OfficeChromatography/2LabsToGo-Eco-Test/2LabsToGo-Eco-Hardware/Material-Lists/Prusa-basket.xlsx

Prusa basket
Amount | Part description | Unit price | Total price EUR
1 | Stepper motor Z-axis Right (MK3/S/+, MK2.5/S, MK2/S) | 32.68 | 32.68
1 | Hotend PTFE tube (MK2.5S, MK3S, MMU2S) | 1.08 | 1.08
2 | Timing pulley T16-2GT | 2.59 | 5.18
1 | Timing belt 2GT X-axis, MK3 | 4.87 | 4.87
1 | Timing belt 2GT X-axis, MINI | 3.35 | 3.35
1 | Trapezoid nut (i3, MK4, MMU2/2S/3) | 5.86 | 5.86
 |  | total | 53.02
 |  | incl. VAT | 63.09
