OfficeChromatography/2LabsToGo-Eco-Test/2LabsToGo-Eco-Hardware/Electronics/Digikey-basket_mainboard_plugs+cables_03-2026.xlsx

Digi-Key: Shopping Cart
Index | Quantity | Part Number | Manufacturer Part Number | Description | Customer Reference | Available | Backorder | Unit Price | Extended Price EUR
1 | 5 | 609-69145-206LF-ND | 69145-206LF | CONN SHUNT .100" 6POS GOLD | mumper motor driver | 5 | 0 | 0.59 | 2.95
2 | 1 | 609-69145-108LF-ND | 69145-108LF | JUMPER LOW PRO DR MULTI | jumper ISP to Pi | 1 | 0 | 1.22 | 1.22
3 | 1 | IDSD-20-D-02.00-ND | IDSD-20-D-02.00 | INSULATION DISPLACEMENT TERMINAL | GPIO cable | 0 | 1 | 12.35 | 12.35
4 | 1 | IDSS-14-D-05.00-ND | IDSS-14-D-05.00 | INSULATION DISPLACEMENT SOCKET C | Status LED board cable | 0 | 1 | 6.79 | 6.79
5 | 1 | 609-3887-ND | TJ0451560000G | TERM BLOCK PLUG 4POS 5.08MM | external port | 1 | 0 | 1.7 | 1.70
6 | 1 | 277-1164-ND | 1803604 | TERM BLOCK PLUG 5POS 3.81MM | plate holder | 1 | 0 | 5.21 | 5.21
7 | 1 | 277-1166-ND | 1803620 | TERM BLOCK PLUG 7POS 3.81MM | plug LEDs | 1 | 0 | 7.07 | 7.07
8 | 5 | 277-1161-ND | 1803578 | TERM BLOCK PLUG 2POS 3.81MM | pump, valves, light, nebulizer | 5 | 0 | 2.32 | 11.60
9 | 1 | 277-2414-ND | 1840405 | TERM BLOCK PLUG 6POS 3.50MM | plug mini-incubator | 1 | 0 | 6.75 | 6.75
