OfficeChromatography/2LabsToGo-Eco-Test/2LabsToGo-Eco-Hardware/Electronics/Digikey-basket_status-LED-board_03-2026.xlsx

Digi-Key: Shopping Cart
Index | Quantity | Part Number | Manufacturer Part Number | Description | Customer Reference | Available | Backorder | Unit Price | Extended Price EUR
1 | 3 | 754-1131-1-ND | APT2012SGC | LED GREEN CLEAR CHIP SMD | LED1, LED2, LED3 | 3 | 0 | 0.16 | 0.48
2 | 6 | 754-1133-1-ND | APT2012SURCK | LED RED CLEAR CHIP SMD | LED4, LED5, LED6, LED8, LED9, LED10 | 6 | 0 | 0.17 | 1.02
3 | 2 | 754-1134-1-ND | APT2012SYCK | LED YELLOW CLEAR CHIP SMD | LED7, LED11 | 0 | 2 | 0.17 | 0.34
4 | 1 | 19-Y2514-6002-SH14PSTHDR0.112GF-ND | Y2514-6002-SH 14P ST HDR 0.112 GF | 3M FOUR-WALL HEADER 2500 SERIES | SV1 | 1 | 0 | 1.02 | 1.02
