OfficeChromatography/2LabsToGo-Eco-Test/2LabsToGo-Eco-Hardware/Electronics/Digikey-basket_UV-LED-boards_03-2026.xlsx

Digi-Key: Warenkorb
Index | Menge | Teilenummer | Hersteller-Teilenummer | Beschreibung | Kundenreferenz | Verfügbar | Lieferrückstände | Stückpreis | Gesamtpreis EUR
1 | 4 | 1830-1187-1-ND | IN-C33CTNU2 | TOP VIEW 3535 3.5X3.5X2.0 | UV 365 nm LEDs | 4 | 0 | 5.92 | 23.68
2 | 4 | 4515-SA265-35030-SA1CT-ND | SA265-35030-SA1 | 260 - 270 NM, >30MW OUTPUT POWER | UV 265 nm LEDs | 4 | 0 | 3.85 | 15.40
3 | 10 | P17615CT-ND | ERJ-8BQF4R3V | RES SMD 4.3 OHM 1% 1/2W 1206 | UV 365 board, 8 needed | 10 | 0 | 0.124 | 1.24
4 | 10 | P20.0FCT-ND | ERJ-8ENF20R0V | RES SMD 20 OHM 1% 1/4W 1206 | UV 265 board, 4 needed | 10 | 0 | 0.07 | 0.70
