OfficeChromatography/2LabsToGo-Eco-Test/2LabsToGo-Eco-Hardware/3D-Parts/STL/tools/tool_ miniature_ball_ bearings.stl

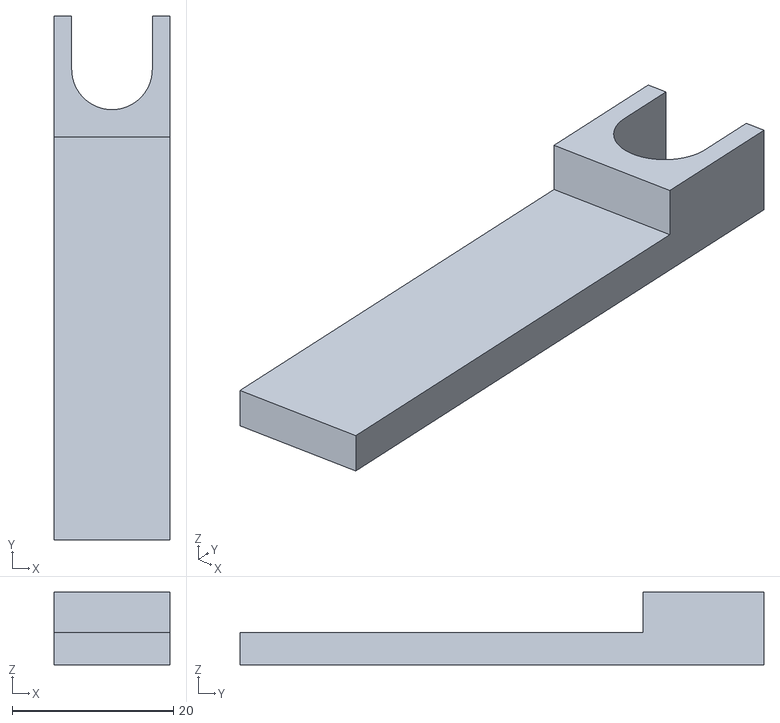
[picture p18: CAD file, 2026-04-15]
2LabsToGo-Eco-Hardware/3D-Parts/STL/tools/tool_ miniature_ball_ bearings.stl
14.4 x 65.0 x 9.00
