OfficeChromatography/2LabsToGo-Eco-Test/2LabsToGo-Eco-Hardware/3D-Parts/STL/x-axis/x-axis_cart-tensioner.stl

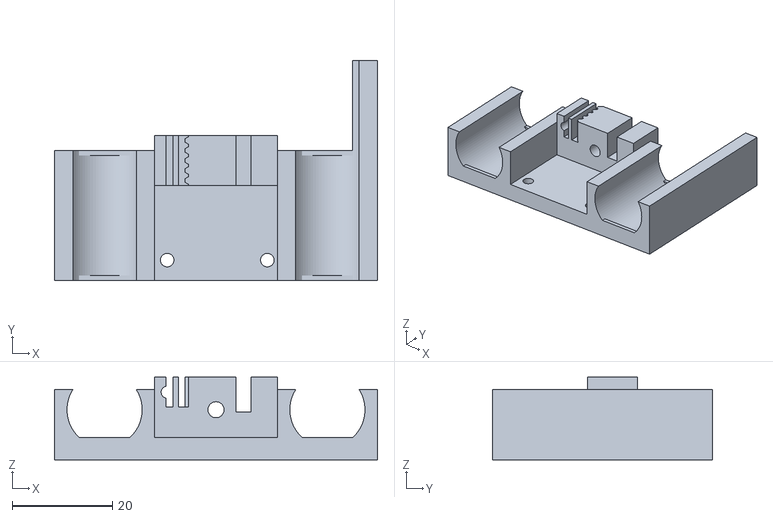
[picture p19: CAD file, 2026-04-15]
2LabsToGo-Eco-Hardware/3D-Parts/STL/x-axis/x-axis_cart-tensioner.stl
64.5 x 44.0 x 16.5
