OfficeChromatography/2LabsToGo-Eco-Test/2LabsToGo-Eco-Hardware/3D-Parts/STL/y-axis/y-axis_tensioner.stl

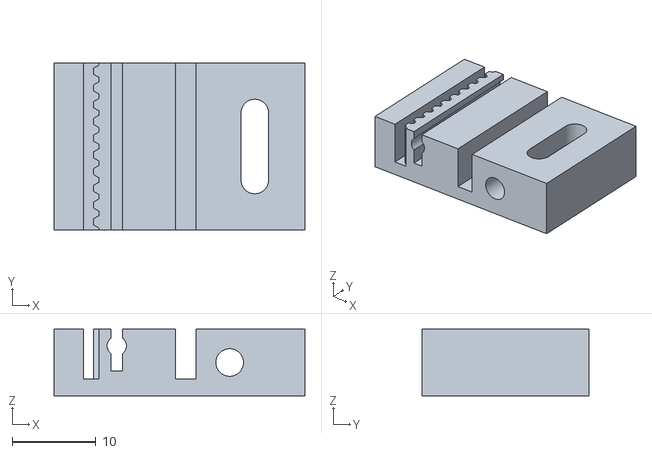
[picture p20: CAD file, 2026-04-15]
2LabsToGo-Eco-Hardware/3D-Parts/STL/y-axis/y-axis_tensioner.stl
30.0 x 20.0 x 8.00
