OfficeChromatography/2LabsToGo-Eco-Test/2LabsToGo-Eco-Hardware/3D-Parts/Aluminum-plates/alu-plate_plate-holder.step

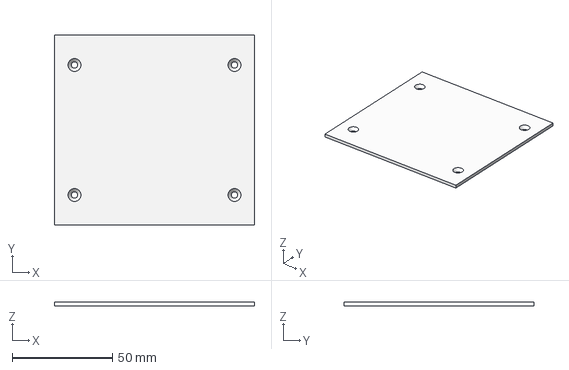
[picture p21: CAD file, 2026-04-15]
2LabsToGo-Eco-Hardware/3D-Parts/Aluminum-plates/alu-plate_plate-holder.step
100.0 x 95.0 x 2.00 mm
