OfficeChromatography/2LabsToGo-Eco-Test/2LabsToGo-Eco-Hardware/3D-Parts/DXF-panels/front.dxf

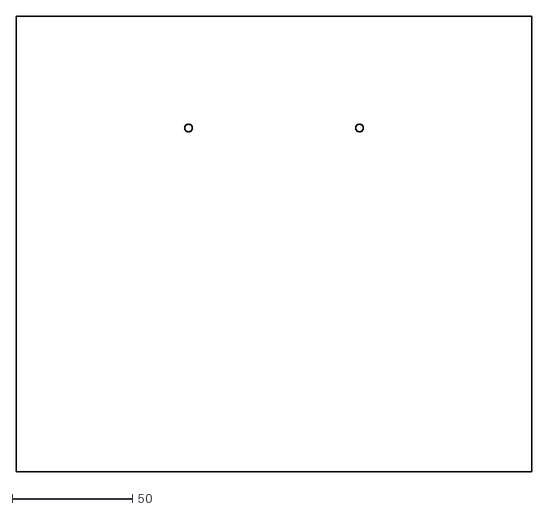
[picture p22: CAD file, 2026-04-15]
2LabsToGo-Eco-Hardware/3D-Parts/DXF-panels/front.dxf
214.0 x 189.0
