OfficeChromatography/2LabsToGo-Eco-Test/2LabsToGo-Eco-Hardware/3D-Parts/STL/autosampler/rinsing_vial.stl

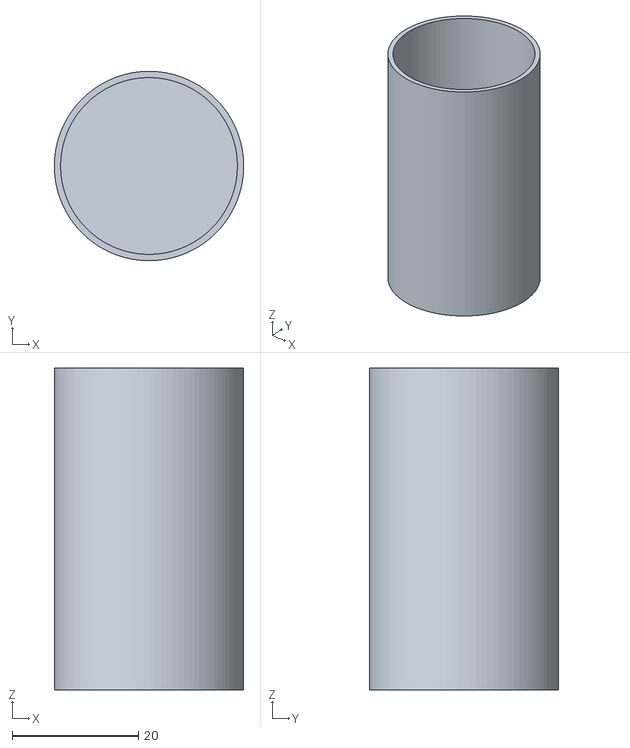
[picture p23: CAD file, 2026-04-15]
2LabsToGo-Eco-Hardware/3D-Parts/STL/autosampler/rinsing_vial.stl
30.0 x 30.0 x 51.0
