OfficeChromatography/2LabsToGo-Eco-Test/2LabsToGo-Eco-Hardware/3D-Parts/STL/camera_cabinet/camera_cabinet_top.stl

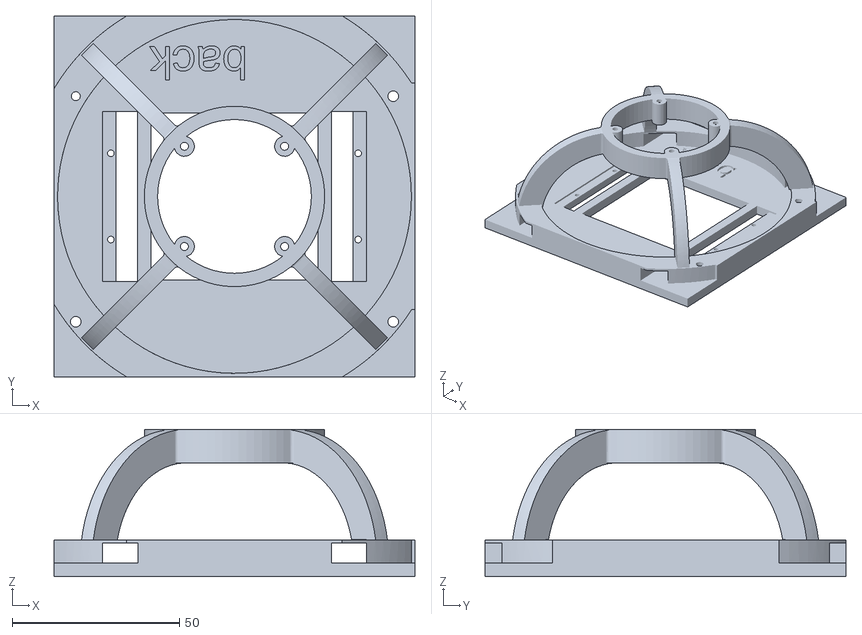
[picture p24: CAD file, 2026-04-15]
2LabsToGo-Eco-Hardware/3D-Parts/STL/camera_cabinet/camera_cabinet_top.stl
108.0 x 108.1 x 44.0
