OfficeChromatography/2LabsToGo-Eco-Test/2LabsToGo-Eco-Hardware/3D-Parts/STL/DC-power-jacket_housing/DC-power-jacket_housing_cover.stl

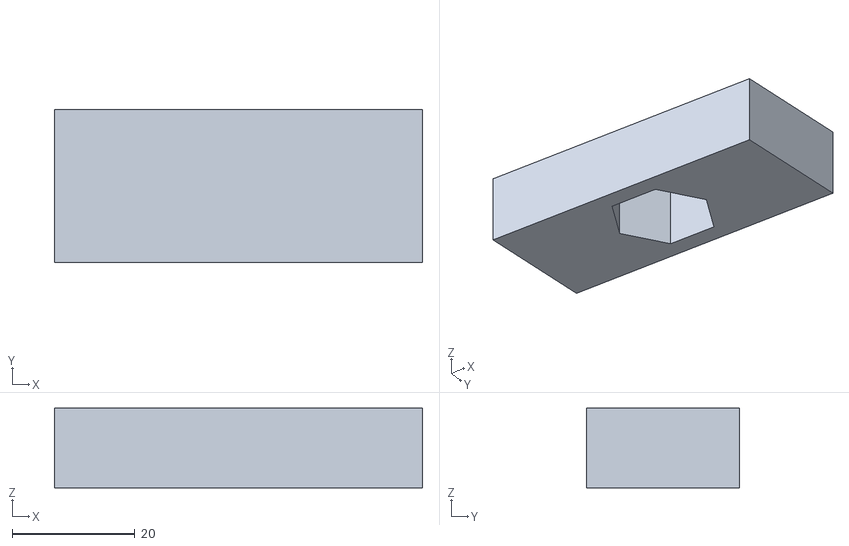
[picture p25: CAD file, 2026-04-15]
2LabsToGo-Eco-Hardware/3D-Parts/STL/DC-power-jacket_housing/DC-power-jacket_housing_cover.stl
60.0 x 25.0 x 13.0
