OfficeChromatography/2LabsToGo-Eco-Test/2LabsToGo-Eco-Hardware/3D-Parts/STL/e-axis/e-axis_connector_long.stl

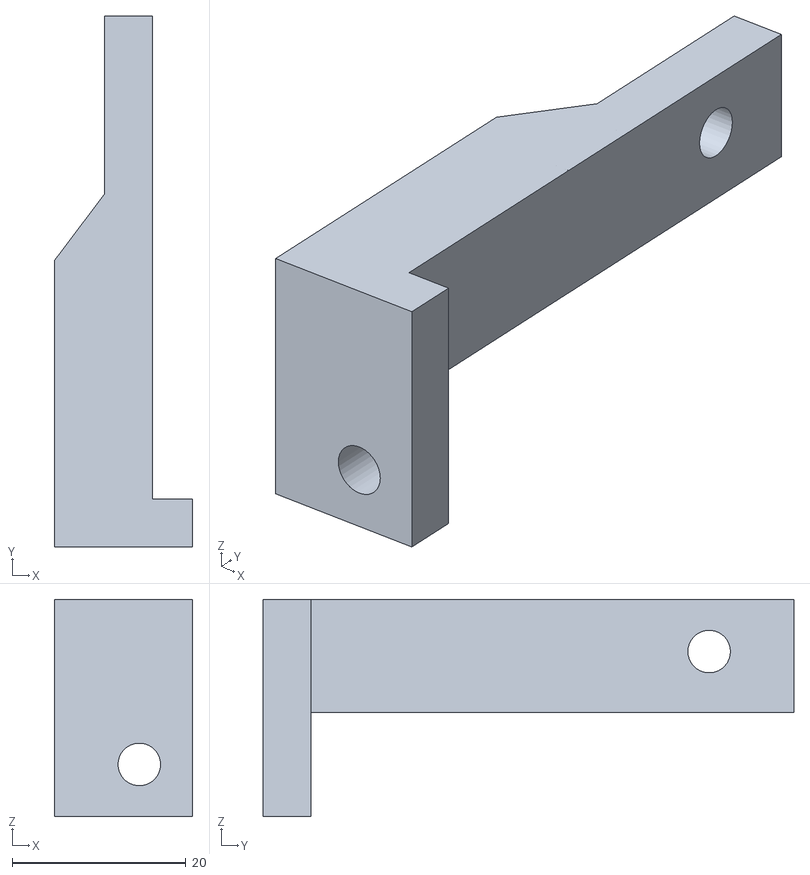
[picture p26: CAD file, 2026-04-15]
2LabsToGo-Eco-Hardware/3D-Parts/STL/e-axis/e-axis_connector_long.stl
15.9 x 61.1 x 25.0
