OfficeChromatography/2LabsToGo-Eco-Test/2LabsToGo-Eco-Hardware/3D-Parts/STL/electronic-box/electronic_box.stl

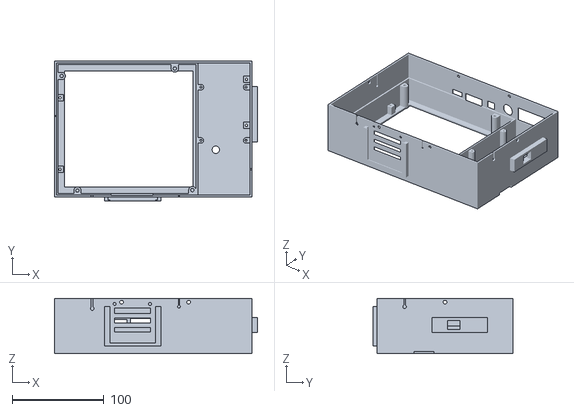
[picture p27: CAD file, 2026-04-20]
2LabsToGo-Eco-Hardware/3D-Parts/STL/electronic-box/electronic_box.stl
221.0 x 152.4 x 60.0
