OfficeChromatography/2LabsToGo-Eco-Test/2LabsToGo-Eco-Hardware/3D-Parts/STL/frames/frame_back_buttom.stl

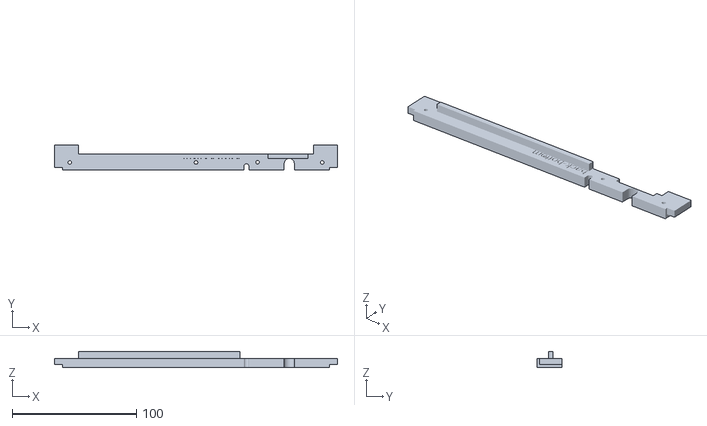
[picture p28: CAD file, 2026-04-20]
2LabsToGo-Eco-Hardware/3D-Parts/STL/frames/frame_back_buttom.stl
227.6 x 20.0 x 13.0
