OfficeChromatography/2LabsToGo-Eco-Test/2LabsToGo-Eco-Hardware/3D-Parts/STL/humidity-control/humidity_control_box-lid.stl

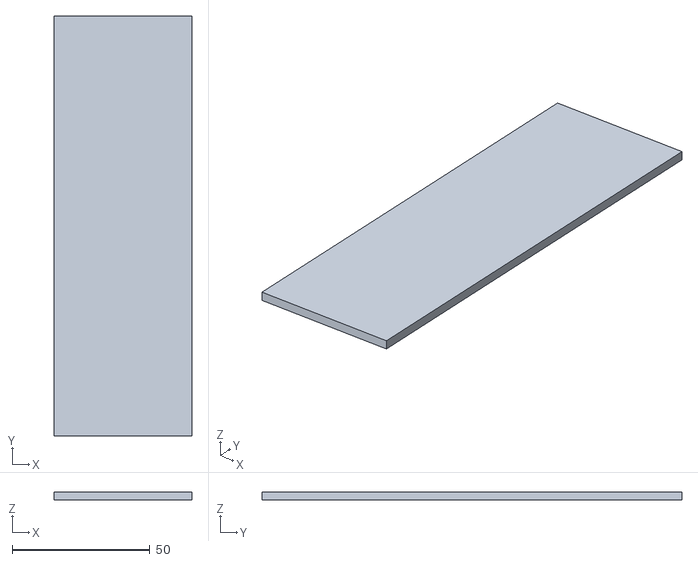
[picture p29: CAD file, 2026-04-15]
2LabsToGo-Eco-Hardware/3D-Parts/STL/humidity-control/humidity_control_box-lid.stl
50.0 x 152.0 x 3.00
