OfficeChromatography/2LabsToGo-Eco-Test/2LabsToGo-Eco-Hardware/3D-Parts/STL/mini-incubator/mini-incubator_inner_lid.stl

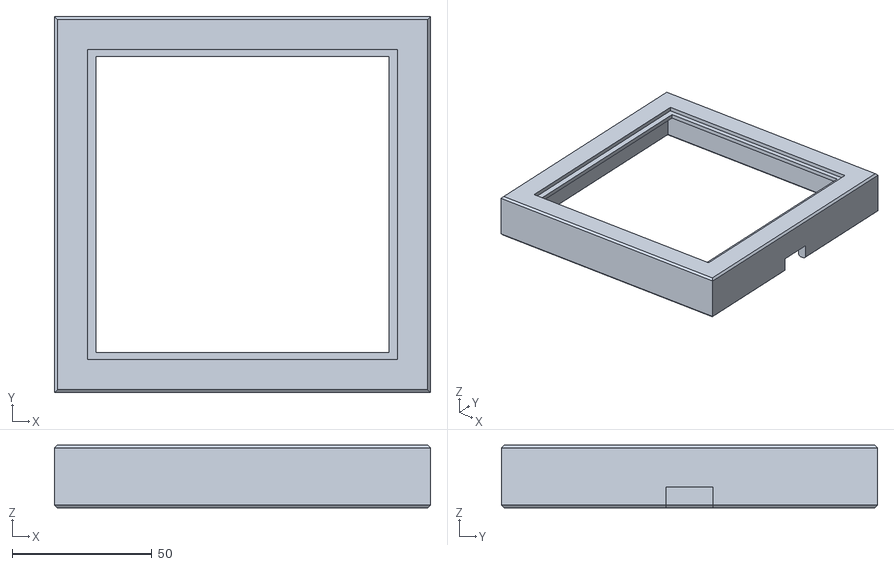
[picture p30: CAD file, 2026-04-15]
2LabsToGo-Eco-Hardware/3D-Parts/STL/mini-incubator/mini-incubator_inner_lid.stl
134.6 x 134.6 x 22.5
