OfficeChromatography/2LabsToGo-Eco-Test/2LabsToGo-Eco-Hardware/3D-Parts/STL/nebulizer/nebulizer_atomizer_part-1.stl

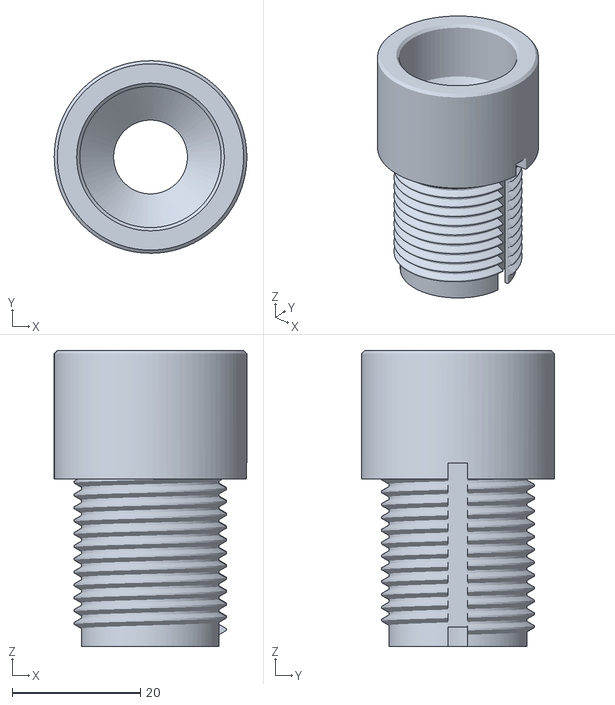
[picture p31: CAD file, 2026-04-20]
2LabsToGo-Eco-Hardware/3D-Parts/STL/nebulizer/nebulizer_atomizer_part-1.stl
30.0 x 30.0 x 46.1
