OfficeChromatography/2LabsToGo-Eco-Test/2LabsToGo-Eco-Hardware/3D-Parts/STL/panels/leg_inside.stl

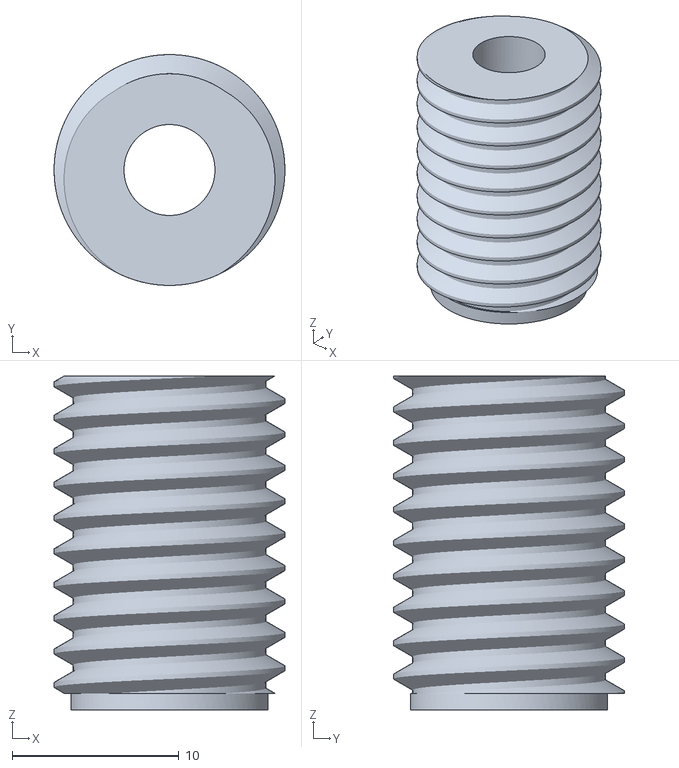
[picture p32: CAD file, 2026-04-15]
2LabsToGo-Eco-Hardware/3D-Parts/STL/panels/leg_inside.stl
13.8 x 13.8 x 20.0
