OfficeChromatography/2LabsToGo-Eco-Test/2LabsToGo-Eco-Hardware/3D-Parts/STL/plate-holder/multifunctional_plate_holder_cover_development.stl

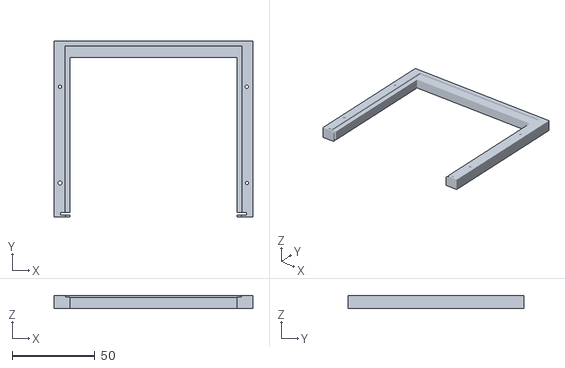
[picture p33: CAD file, 2026-04-15]
2LabsToGo-Eco-Hardware/3D-Parts/STL/plate-holder/multifunctional_plate_holder_cover_development.stl
120.0 x 106.0 x 8.00
