OfficeChromatography/2LabsToGo-Eco-Test/2LabsToGo-Eco-Hardware/3D-Parts/STL/syringe-pump/syringe-pump_clip.stl

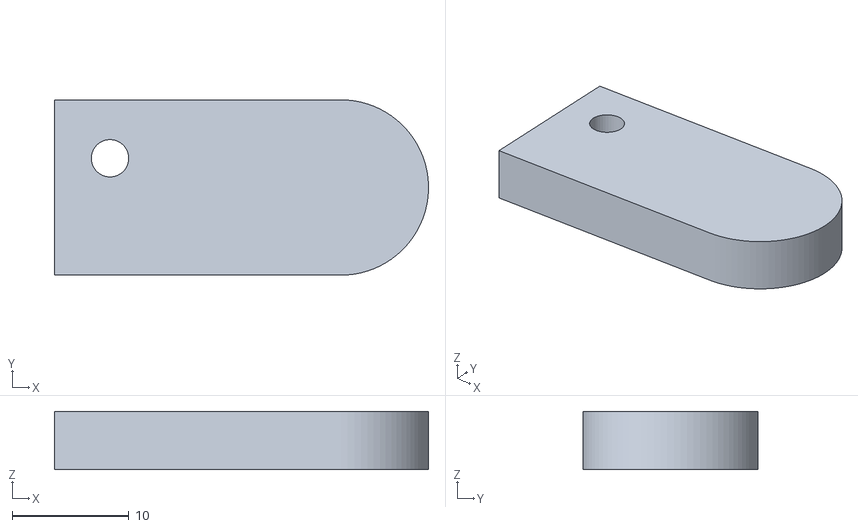
[picture p34: CAD file, 2026-04-15]
2LabsToGo-Eco-Hardware/3D-Parts/STL/syringe-pump/syringe-pump_clip.stl
32.0 x 15.0 x 5.00
