OfficeChromatography/2LabsToGo-Eco-Test/2LabsToGo-Eco-Hardware/3D-Parts/STL/tools/handle_for_thread_tap_M5.stl

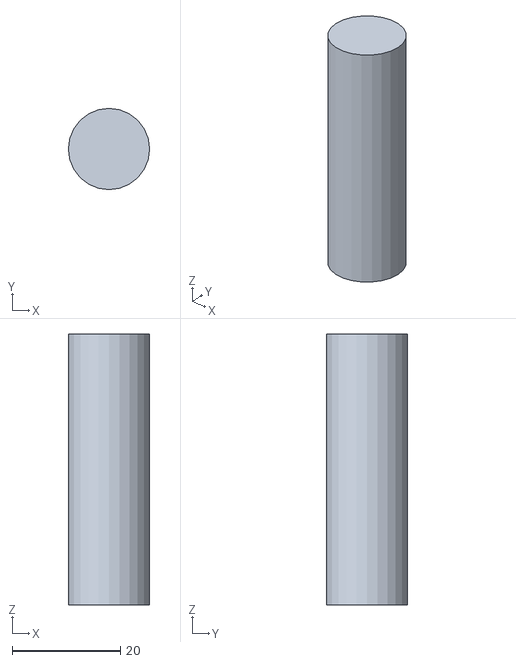
[picture p35: CAD file, 2026-04-15]
2LabsToGo-Eco-Hardware/3D-Parts/STL/tools/handle_for_thread_tap_M5.stl
15.0 x 15.0 x 50.0
