OfficeChromatography/2LabsToGo-Eco-Test/2LabsToGo-Eco-Hardware/3D-Parts/STL/x-axis/x-axis_cable_guide_top_right.stl

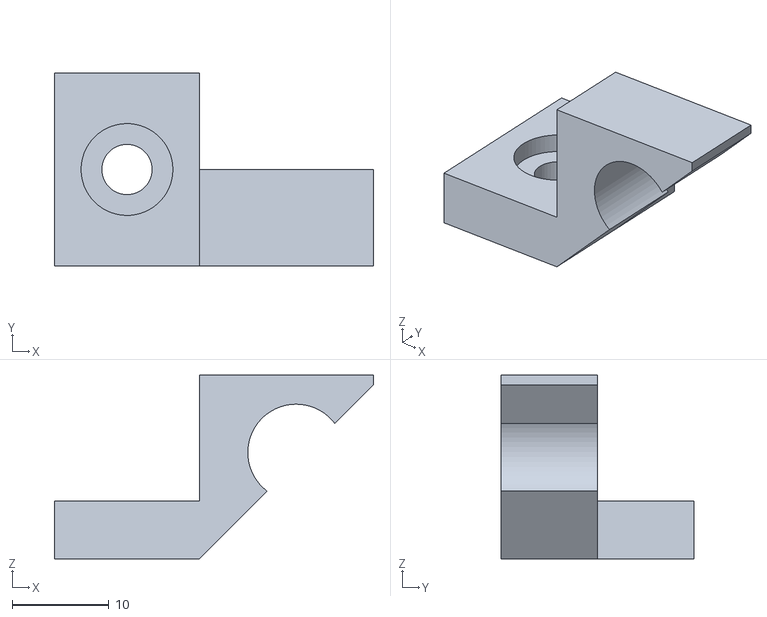
[picture p36: CAD file, 2026-04-15]
2LabsToGo-Eco-Hardware/3D-Parts/STL/x-axis/x-axis_cable_guide_top_right.stl
33.0 x 20.0 x 19.0
