OfficeChromatography/2LabsToGo-Eco-Test/2LabsToGo-Eco-Hardware/3D-Parts/STL/y-axis/y-axis_back.stl

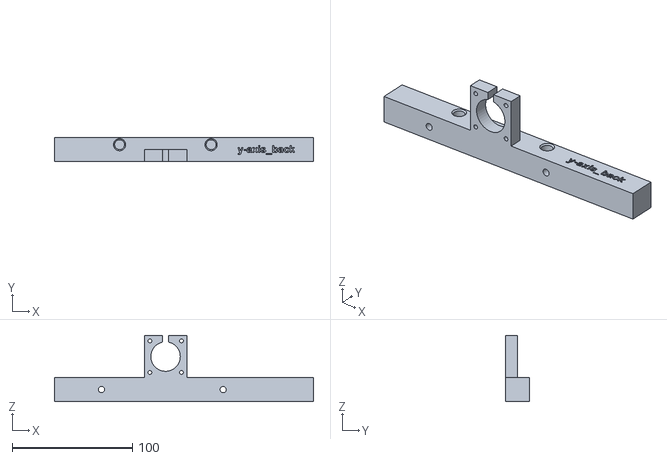
[picture p37: CAD file, 2026-04-15]
2LabsToGo-Eco-Hardware/3D-Parts/STL/y-axis/y-axis_back.stl
215.0 x 20.0 x 55.0
