OfficeChromatography/2LabsToGo-Eco-Test/2LabsToGo-Eco-Hardware/3D-Parts/DXF-panels/top_front.dxf

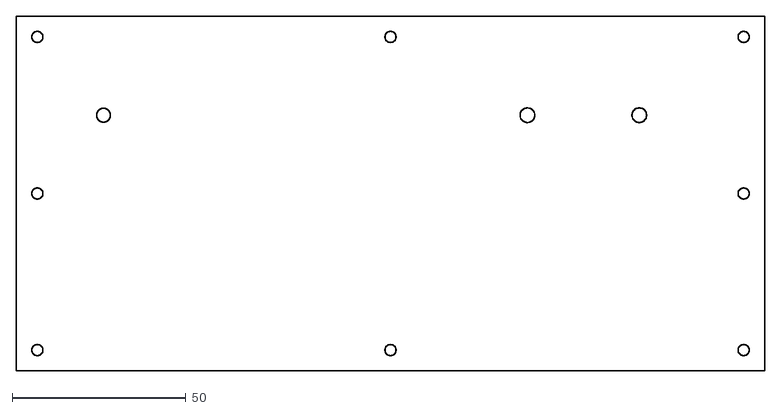
[picture p38: CAD file, 2026-04-15]
2LabsToGo-Eco-Hardware/3D-Parts/DXF-panels/top_front.dxf
215.0 x 102.0
