OfficeChromatography/2LabsToGo-Eco-Test/2LabsToGo-Eco-Hardware/3D-Parts/STL/autosampler/autosampler_distance-tool.stl

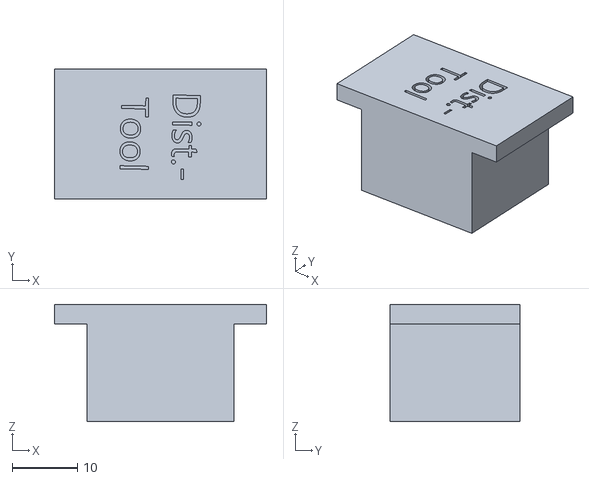
[picture p39: CAD file, 2026-04-15]
2LabsToGo-Eco-Hardware/3D-Parts/STL/autosampler/autosampler_distance-tool.stl
32.5 x 20.0 x 18.0
