OfficeChromatography/2LabsToGo-Eco-Test/2LabsToGo-Eco-Hardware/3D-Parts/STL/camera_cabinet/camera_cabinet.stl

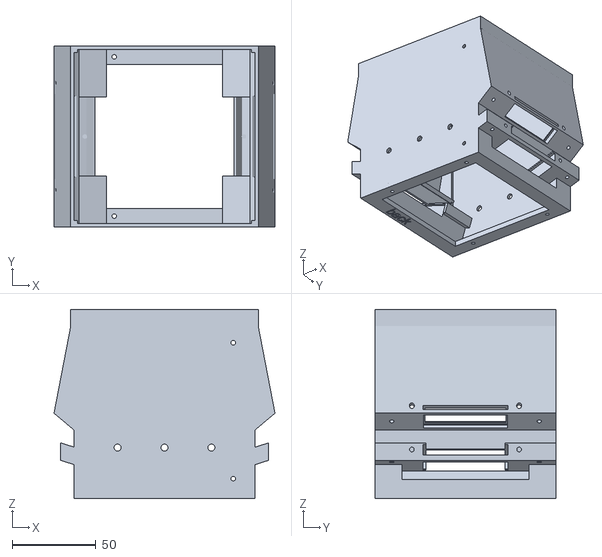
[picture p40: CAD file, 2026-04-15]
2LabsToGo-Eco-Hardware/3D-Parts/STL/camera_cabinet/camera_cabinet.stl
131.8 x 108.0 x 113.0
