OfficeChromatography/2LabsToGo-Eco-Test/2LabsToGo-Eco-Hardware/3D-Parts/STL/e-axis/e-axis_3way_valve_holder.stl

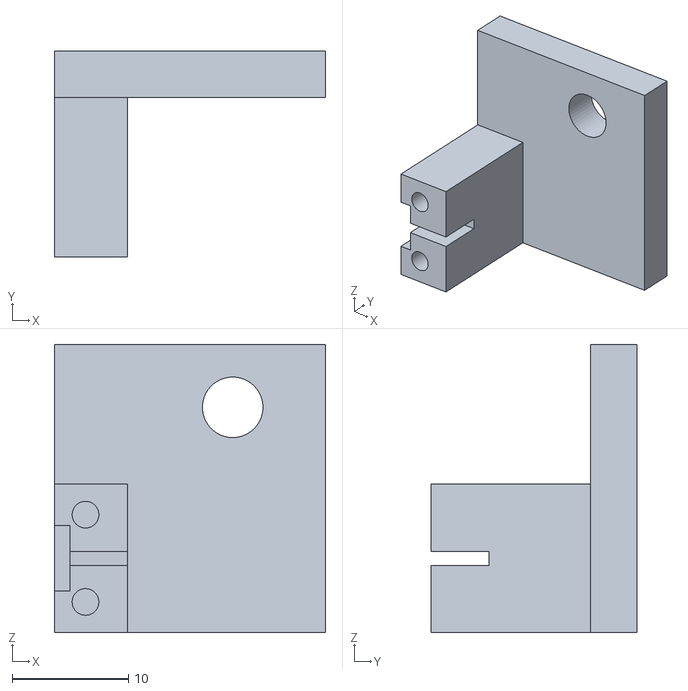
[picture p41: CAD file, 2026-04-15]
2LabsToGo-Eco-Hardware/3D-Parts/STL/e-axis/e-axis_3way_valve_holder.stl
23.3 x 17.7 x 24.8
