OfficeChromatography/2LabsToGo-Eco-Test/2LabsToGo-Eco-Hardware/3D-Parts/STL/electronic-box/electronic_box_frame-part1.stl

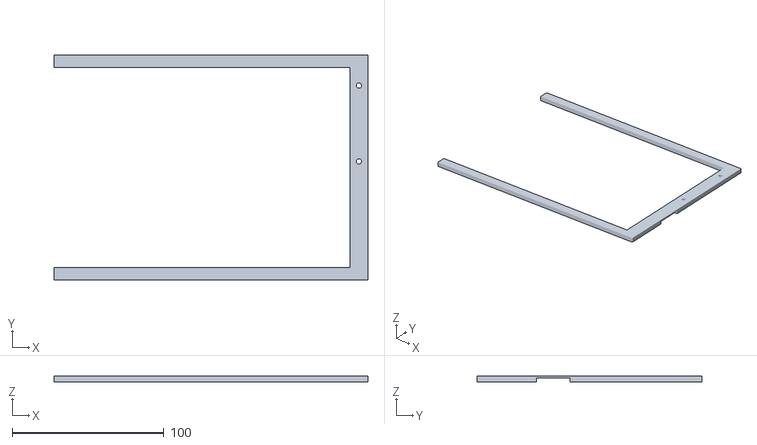
[picture p42: CAD file, 2026-04-20]
2LabsToGo-Eco-Hardware/3D-Parts/STL/electronic-box/electronic_box_frame-part1.stl
207.0 x 148.0 x 4.00
