OfficeChromatography/2LabsToGo-Eco-Test/2LabsToGo-Eco-Hardware/3D-Parts/STL/frames/frame_front.stl

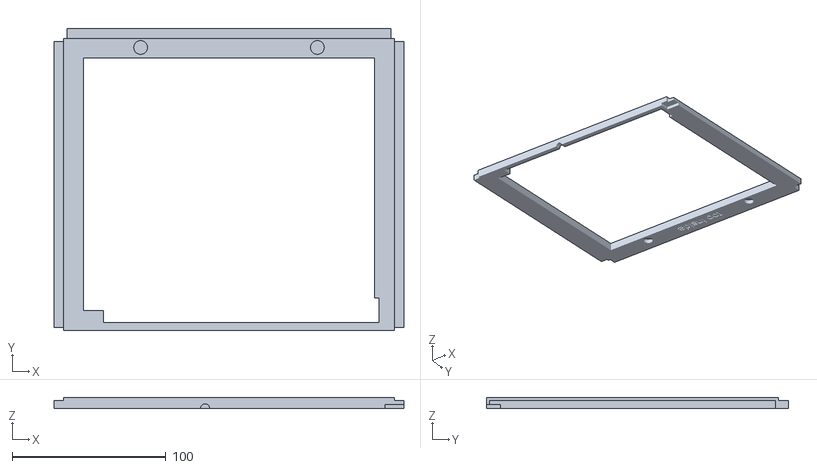
[picture p43: CAD file, 2026-04-15]
2LabsToGo-Eco-Hardware/3D-Parts/STL/frames/frame_front.stl
227.6 x 196.3 x 7.00
