OfficeChromatography/2LabsToGo-Eco-Test/2LabsToGo-Eco-Hardware/3D-Parts/STL/humidity-control/humidity_control_drawer.stl

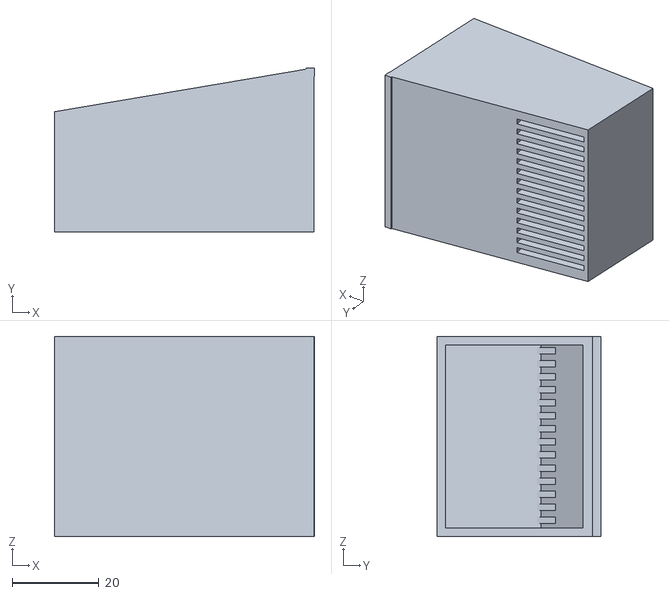
[picture p44: CAD file, 2026-04-15]
2LabsToGo-Eco-Hardware/3D-Parts/STL/humidity-control/humidity_control_drawer.stl
59.8 x 37.8 x 46.0
