OfficeChromatography/2LabsToGo-Eco-Test/2LabsToGo-Eco-Hardware/3D-Parts/STL/mini-incubator/mini-incubator_feet.stl

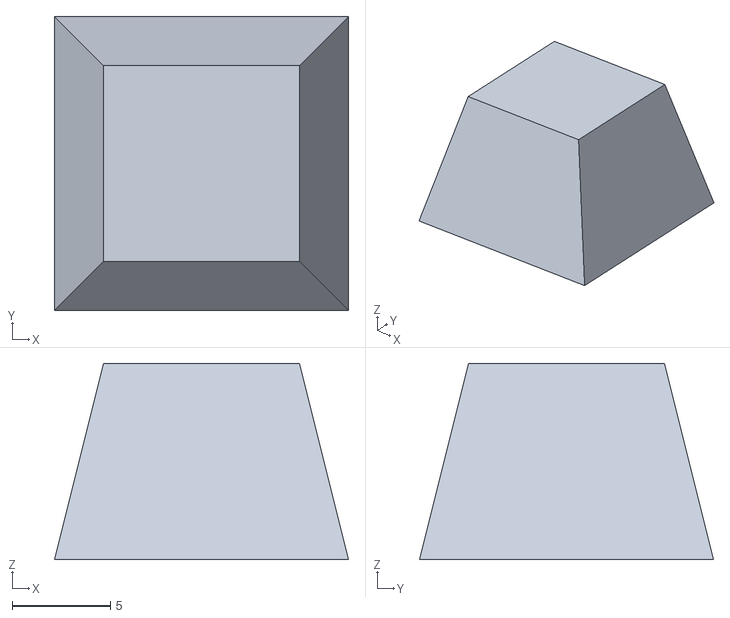
[picture p45: CAD file, 2026-04-15]
2LabsToGo-Eco-Hardware/3D-Parts/STL/mini-incubator/mini-incubator_feet.stl
15.0 x 15.0 x 10.0
