OfficeChromatography/2LabsToGo-Eco-Test/2LabsToGo-Eco-Hardware/3D-Parts/STL/mini-shaker/mini-shaker_hood.stl

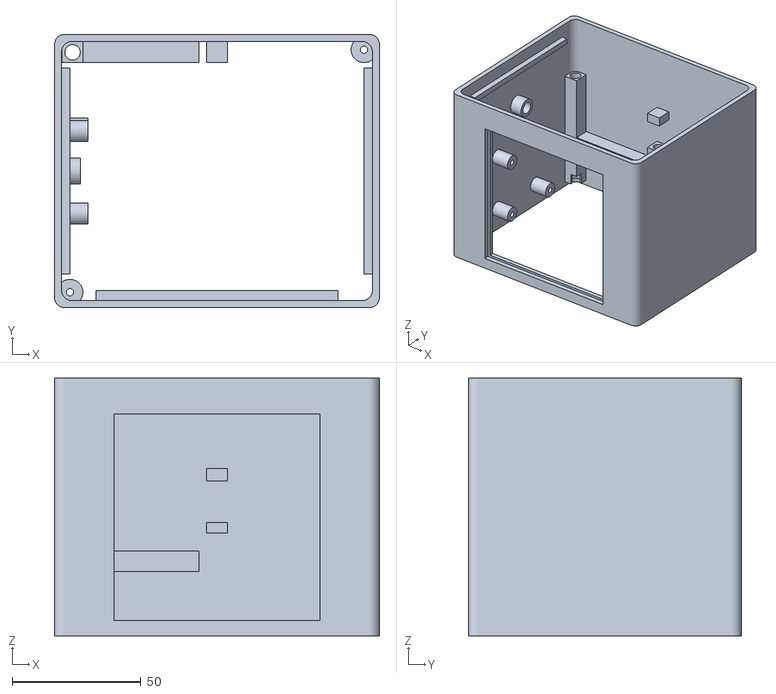
[picture p46: CAD file, 2026-04-15]
2LabsToGo-Eco-Hardware/3D-Parts/STL/mini-shaker/mini-shaker_hood.stl
126.0 x 106.0 x 100.0
