OfficeChromatography/2LabsToGo-Eco-Test/2LabsToGo-Eco-Hardware/3D-Parts/STL/nebulizer/nebulizer_atomizer_part-2.stl

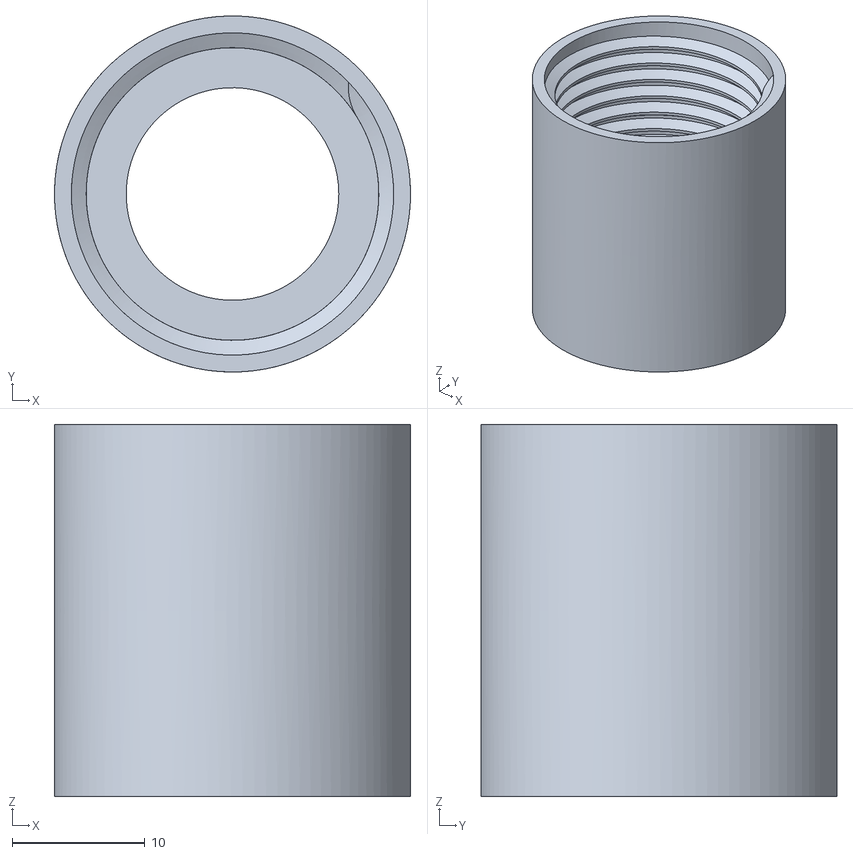
[picture p47: CAD file, 2026-04-20]
2LabsToGo-Eco-Hardware/3D-Parts/STL/nebulizer/nebulizer_atomizer_part-2.stl
26.8 x 26.8 x 28.0
