OfficeChromatography/2LabsToGo-Eco-Test/2LabsToGo-Eco-Hardware/3D-Parts/STL/panels/cover_z1_motor.stl

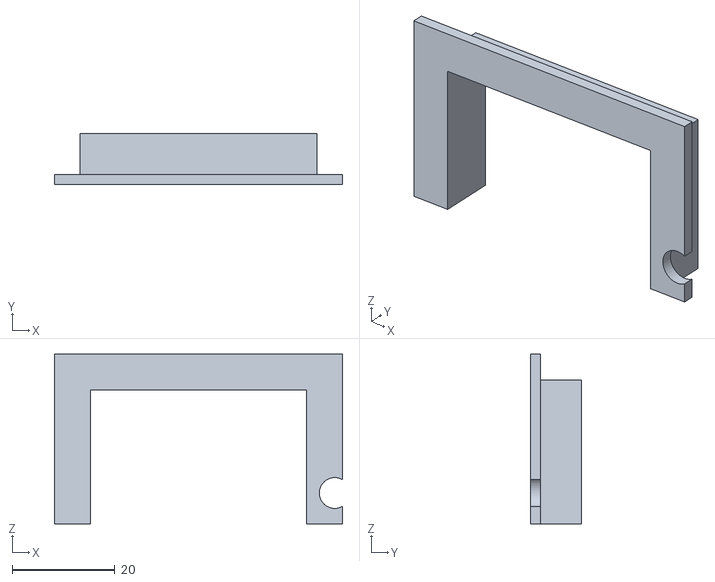
[picture p48: CAD file, 2026-04-15]
2LabsToGo-Eco-Hardware/3D-Parts/STL/panels/cover_z1_motor.stl
56.0 x 10.0 x 33.0
