OfficeChromatography/2LabsToGo-Eco-Test/2LabsToGo-Eco-Hardware/3D-Parts/STL/plate-holder/plate-holder_backlight_front.stl

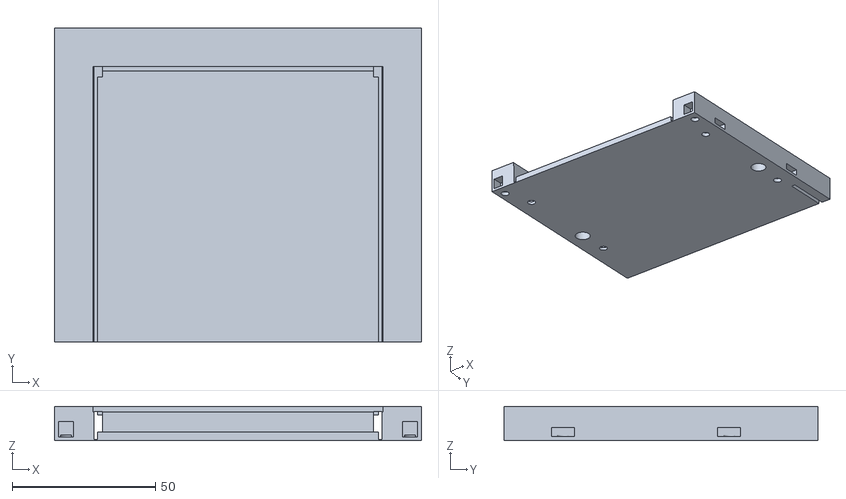
[picture p49: CAD file, 2026-04-15]
2LabsToGo-Eco-Hardware/3D-Parts/STL/plate-holder/plate-holder_backlight_front.stl
128.0 x 109.5 x 12.0
