OfficeChromatography/2LabsToGo-Eco-Test/2LabsToGo-Eco-Hardware/3D-Parts/STL/syringe-pump/syringe-pump_pusher_base.stl

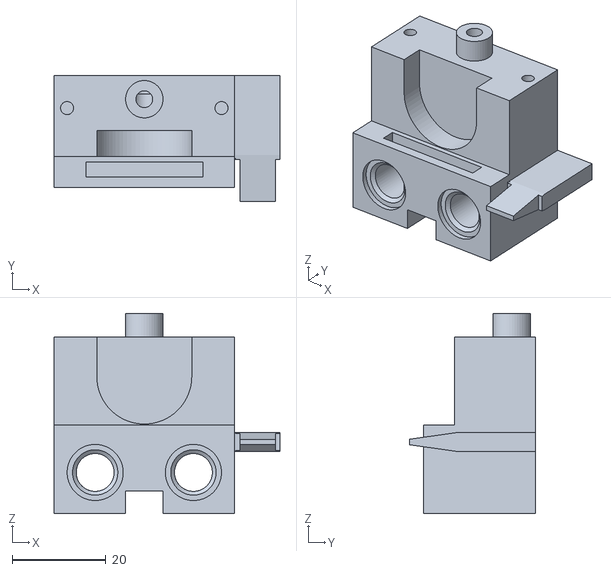
[picture p50: CAD file, 2026-04-15]
2LabsToGo-Eco-Hardware/3D-Parts/STL/syringe-pump/syringe-pump_pusher_base.stl
48.3 x 27.0 x 42.8
