OfficeChromatography/2LabsToGo-Eco-Test/2LabsToGo-Eco-Hardware/3D-Parts/STL/tools/needle-wrench_round.stl

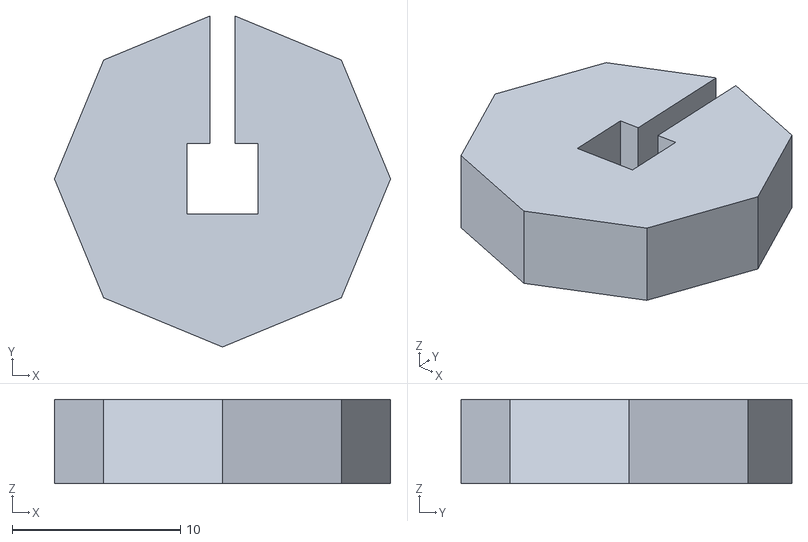
[picture p51: CAD file, 2026-04-15]
2LabsToGo-Eco-Hardware/3D-Parts/STL/tools/needle-wrench_round.stl
20.0 x 19.7 x 5.00
