OfficeChromatography/2LabsToGo-Eco-Test/2LabsToGo-Eco-Hardware/3D-Parts/STL/x-axis/x-axis_right.stl

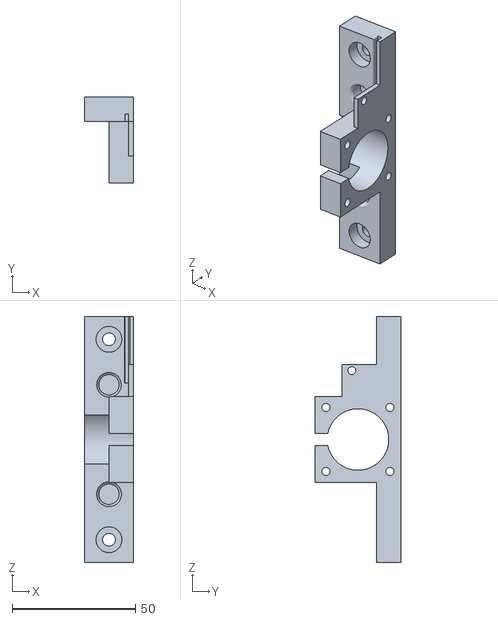
[picture p52: CAD file, 2026-04-15]
2LabsToGo-Eco-Hardware/3D-Parts/STL/x-axis/x-axis_right.stl
20.0 x 35.0 x 100.0
