OfficeChromatography/2LabsToGo-Eco-Test/2LabsToGo-Eco-Hardware/3D-Parts/STL/y-axis/cork.stl

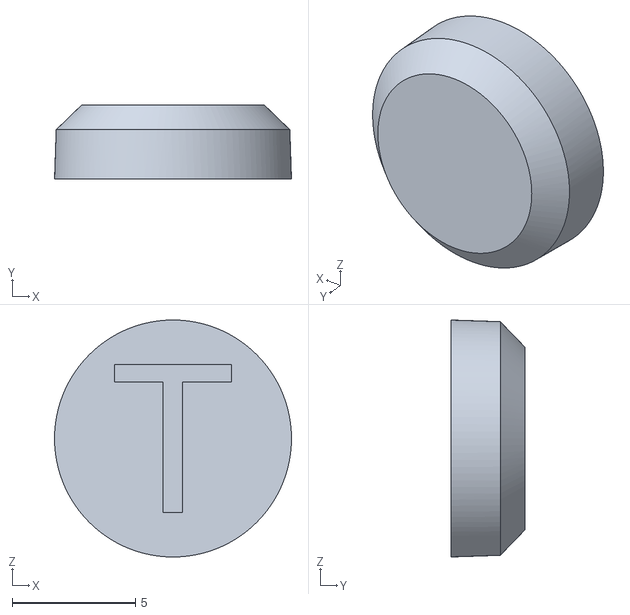
[picture p53: CAD file, 2026-04-15]
2LabsToGo-Eco-Hardware/3D-Parts/STL/y-axis/cork.stl
9.60 x 3.00 x 9.60
