OfficeChromatography/2LabsToGo-Eco-Test/2LabsToGo-Eco-Hardware/3D-Parts/DXF-panels/back.dxf

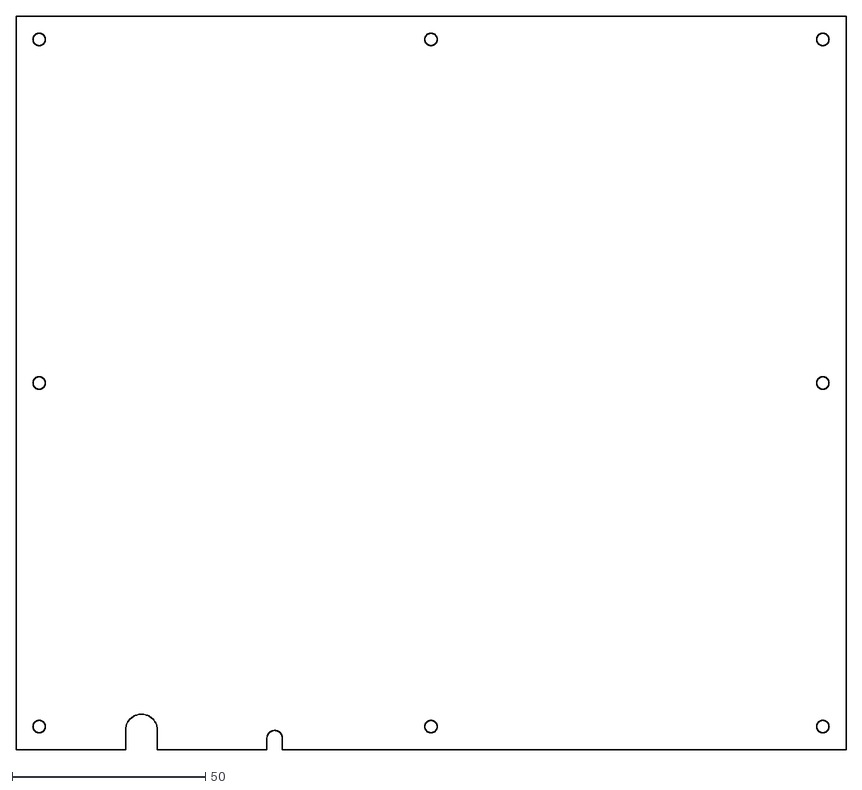
[picture p54: CAD file, 2026-04-15]
2LabsToGo-Eco-Hardware/3D-Parts/DXF-panels/back.dxf
215.0 x 190.0
