OfficeChromatography/2LabsToGo-Eco-Test/2LabsToGo-Eco-Hardware/3D-Parts/STL/autosampler/autosampler_slider_tip.stl

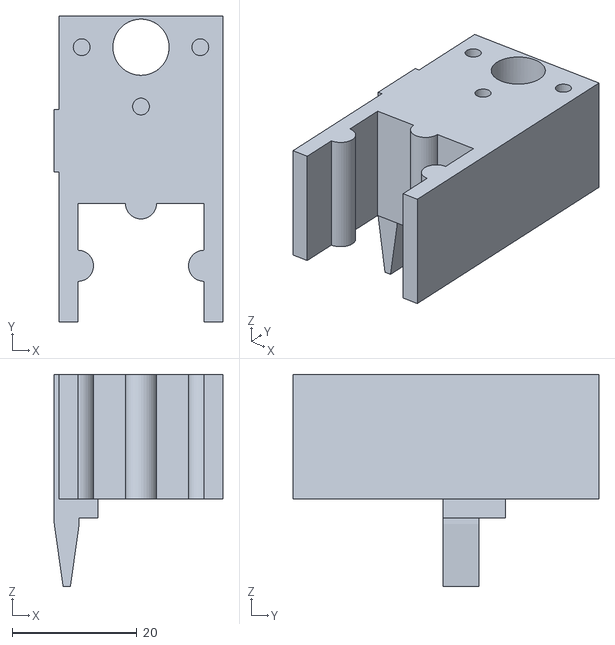
[picture p55: CAD file, 2026-04-15]
2LabsToGo-Eco-Hardware/3D-Parts/STL/autosampler/autosampler_slider_tip.stl
27.0 x 49.0 x 34.0
