OfficeChromatography/2LabsToGo-Eco-Test/2LabsToGo-Eco-Hardware/3D-Parts/STL/camera_cabinet/camera-cabinet_holder.stl

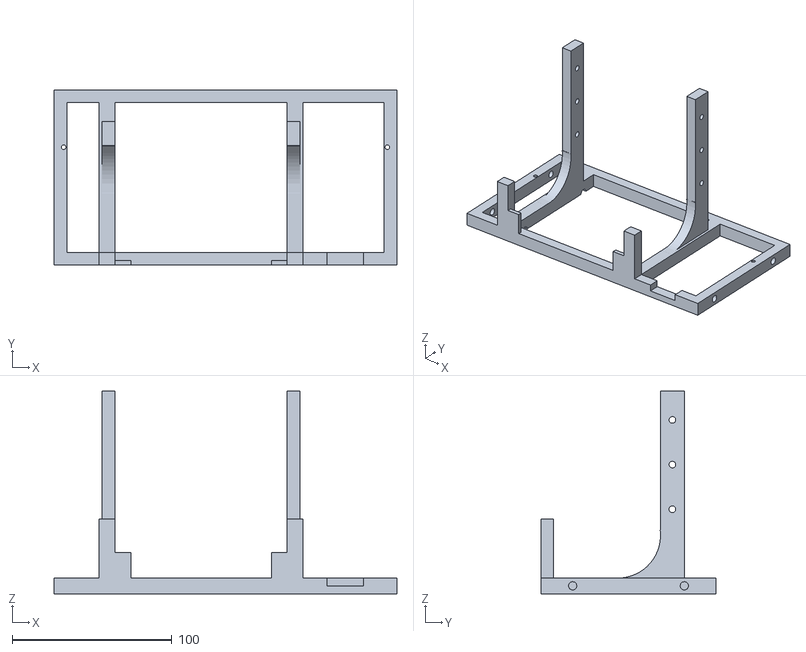
[picture p56: CAD file, 2026-04-15]
2LabsToGo-Eco-Hardware/3D-Parts/STL/camera_cabinet/camera-cabinet_holder.stl
215.0 x 110.0 x 127.0
