OfficeChromatography/2LabsToGo-Eco-Test/2LabsToGo-Eco-Hardware/3D-Parts/STL/e-axis/e-axis_needle_pusher.stl

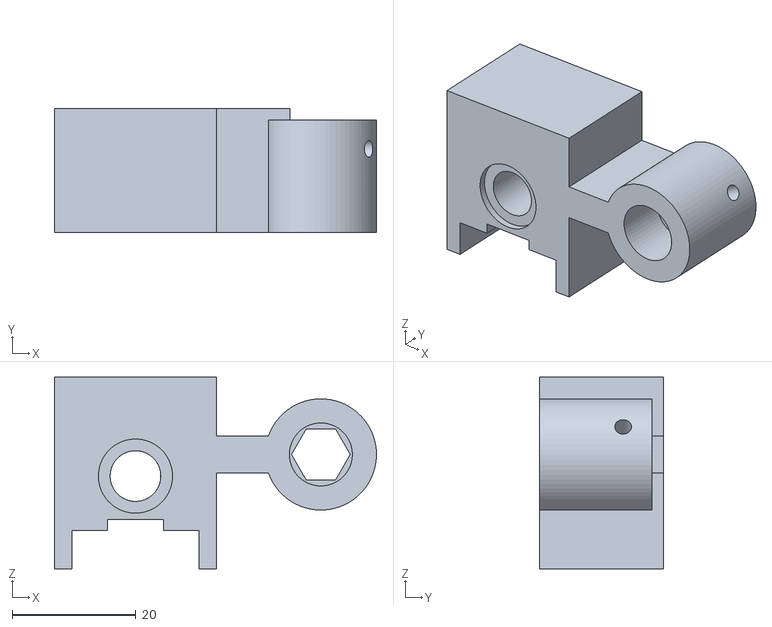
[picture p57: CAD file, 2026-04-15]
2LabsToGo-Eco-Hardware/3D-Parts/STL/e-axis/e-axis_needle_pusher.stl
52.1 x 20.0 x 31.0
