OfficeChromatography/2LabsToGo-Eco-Test/2LabsToGo-Eco-Hardware/3D-Parts/STL/electronic-box/electronic-box_cover.stl

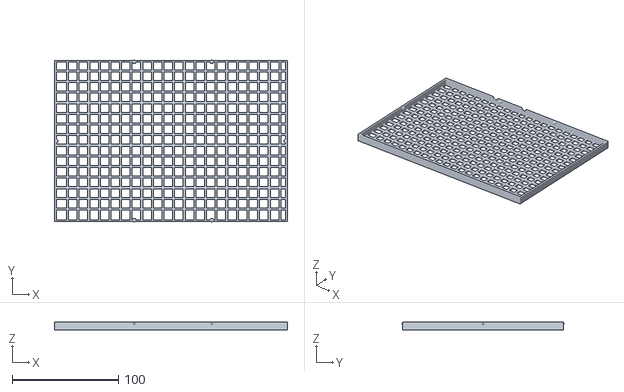
[picture p58: CAD file, 2026-04-15]
2LabsToGo-Eco-Hardware/3D-Parts/STL/electronic-box/electronic-box_cover.stl
219.5 x 152.5 x 8.00
