OfficeChromatography/2LabsToGo-Eco-Test/2LabsToGo-Eco-Hardware/3D-Parts/STL/humidity-control/humidity_control_drawer-handle.stl

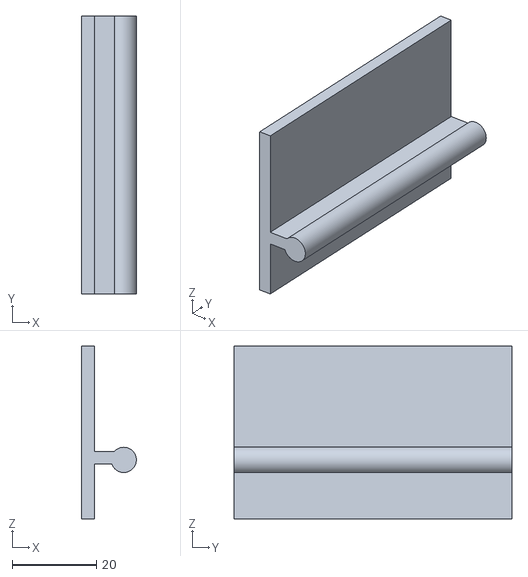
[picture p60: CAD file, 2026-04-15]
2LabsToGo-Eco-Hardware/3D-Parts/STL/humidity-control/humidity_control_drawer-handle.stl
13.0 x 66.0 x 41.0
