OfficeChromatography/2LabsToGo-Eco-Test/2LabsToGo-Eco-Hardware/3D-Parts/STL/mini-incubator/mini-incubator_outer_bottom.stl

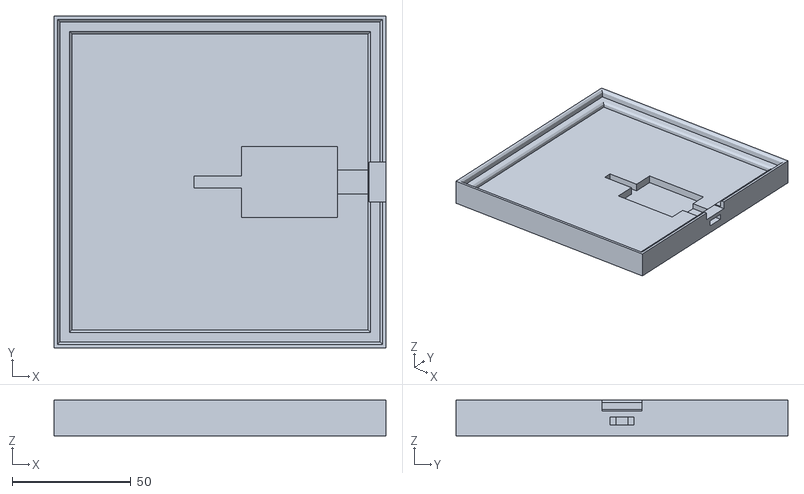
[picture p61: CAD file, 2026-04-15]
2LabsToGo-Eco-Hardware/3D-Parts/STL/mini-incubator/mini-incubator_outer_bottom.stl
140.0 x 140.0 x 15.0
