OfficeChromatography/2LabsToGo-Eco-Test/2LabsToGo-Eco-Hardware/3D-Parts/STL/mini-shaker/heated_hood_cable_support.stl

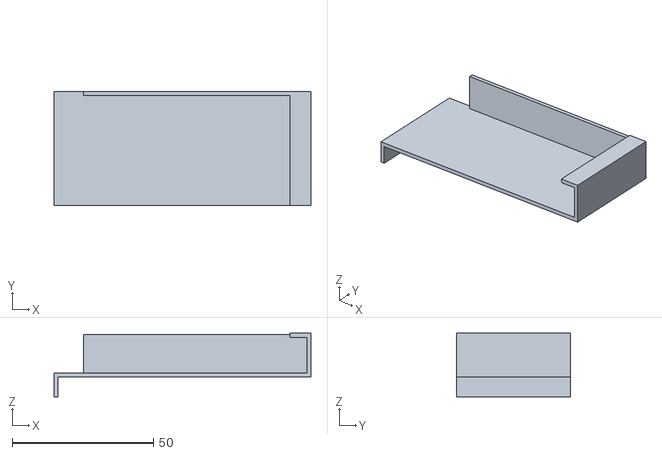
[picture p62: CAD file, 2026-04-15]
2LabsToGo-Eco-Hardware/3D-Parts/STL/mini-shaker/heated_hood_cable_support.stl
91.0 x 40.5 x 22.5
