OfficeChromatography/2LabsToGo-Eco-Test/2LabsToGo-Eco-Hardware/3D-Parts/STL/nebulizer/nebulizer_chamber_lid.stl

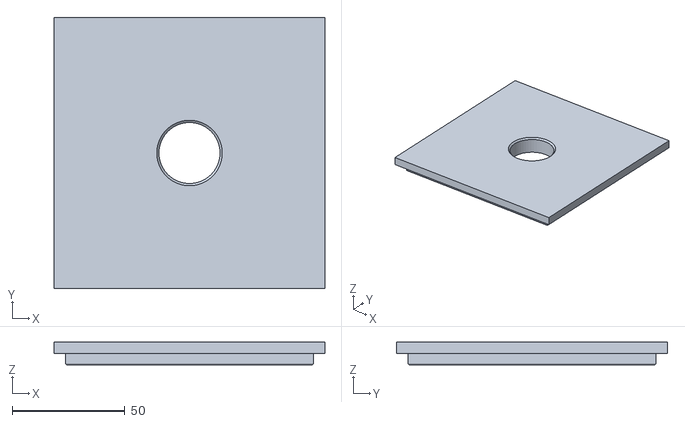
[picture p63: CAD file, 2026-04-15]
2LabsToGo-Eco-Hardware/3D-Parts/STL/nebulizer/nebulizer_chamber_lid.stl
120.0 x 120.0 x 10.0
