OfficeChromatography/2LabsToGo-Eco-Test/2LabsToGo-Eco-Hardware/3D-Parts/STL/panels/cover_autosampler_mounting_profile.stl

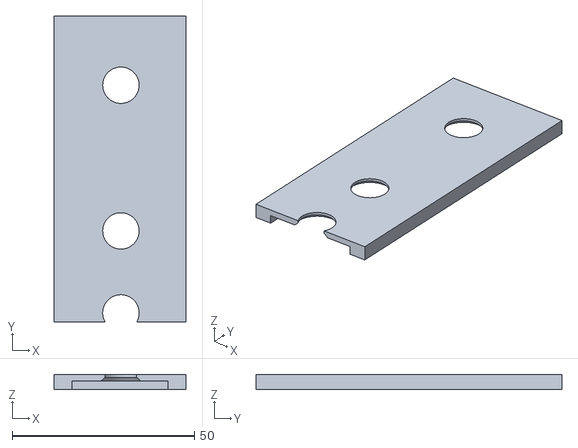
[picture p64: CAD file, 2026-04-15]
2LabsToGo-Eco-Hardware/3D-Parts/STL/panels/cover_autosampler_mounting_profile.stl
36.2 x 84.0 x 4.00
