OfficeChromatography/2LabsToGo-Eco-Test/2LabsToGo-Eco-Hardware/3D-Parts/STL/syringe-pump/syringe-pump_syringe_holder_adapter_5mL.stl

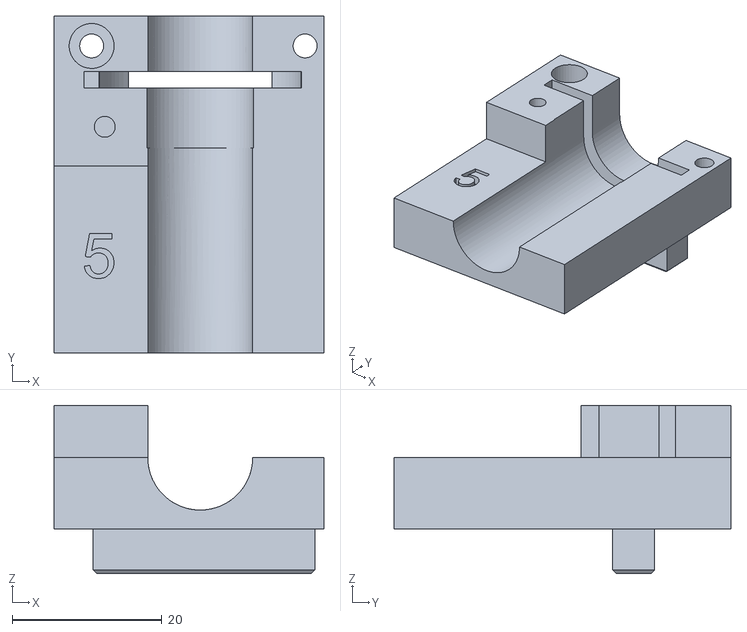
[picture p66: CAD file, 2026-04-15]
2LabsToGo-Eco-Hardware/3D-Parts/STL/syringe-pump/syringe-pump_syringe_holder_adapter_5mL.stl
36.0 x 45.0 x 22.5
