OfficeChromatography/2LabsToGo-Eco-Test/2LabsToGo-Eco-Hardware/3D-Parts/STL/x-axis/x-axis_left.stl

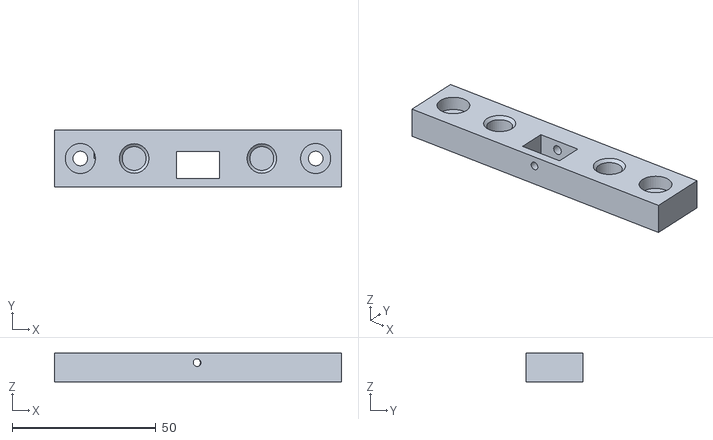
[picture p67: CAD file, 2026-04-15]
2LabsToGo-Eco-Hardware/3D-Parts/STL/x-axis/x-axis_left.stl
100.0 x 20.0 x 10.0
