OfficeChromatography/2LabsToGo-Eco-Test/2LabsToGo-Eco-Hardware/3D-Parts/STL/y-axis/y-axis_cart_tensioner.stl

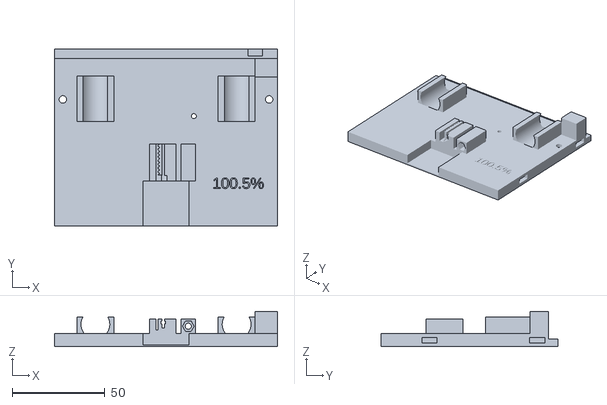
[picture p68: CAD file, 2026-04-15]
2LabsToGo-Eco-Hardware/3D-Parts/STL/y-axis/y-axis_cart_tensioner.stl
120.0 x 95.0 x 19.0
