OfficeChromatography/2LabsToGo-Eco-Test/2LabsToGo-Eco-Hardware/3D-Parts/DXF-panels/side_back.dxf

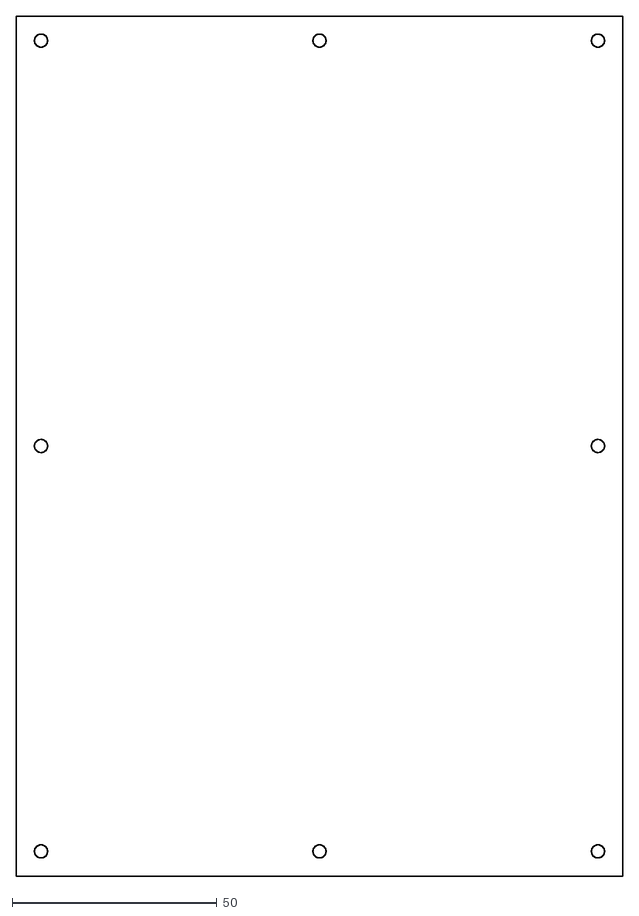
[picture p69: CAD file, 2026-04-15]
2LabsToGo-Eco-Hardware/3D-Parts/DXF-panels/side_back.dxf
148.0 x 210.0
