OfficeChromatography/2LabsToGo-Eco-Test/2LabsToGo-Eco-Hardware/3D-Parts/STL/autosampler/autosampler_vialrack_holder.stl

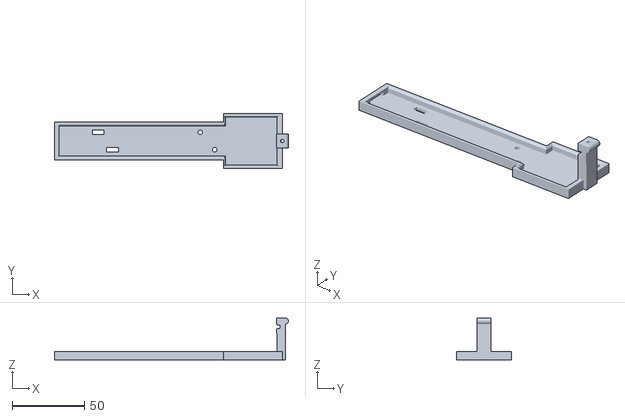
[picture p70: CAD file, 2026-04-15]
2LabsToGo-Eco-Hardware/3D-Parts/STL/autosampler/autosampler_vialrack_holder.stl
162.2 x 38.0 x 29.1
