OfficeChromatography/2LabsToGo-Eco-Test/2LabsToGo-Eco-Hardware/3D-Parts/STL/camera_cabinet/camera_module3_adapter.stl

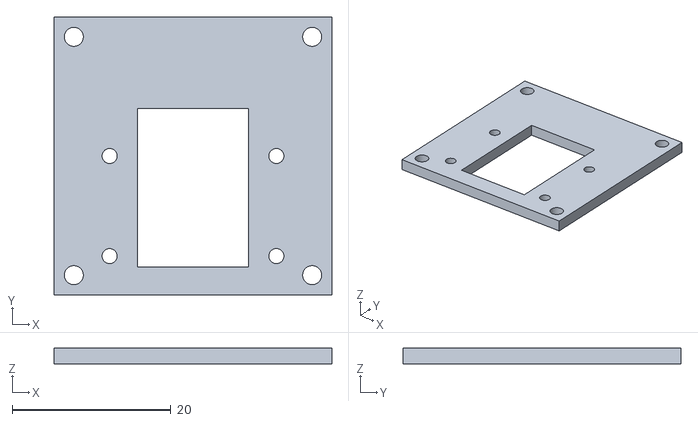
[picture p71: CAD file, 2026-04-15]
2LabsToGo-Eco-Hardware/3D-Parts/STL/camera_cabinet/camera_module3_adapter.stl
35.0 x 35.0 x 2.00
