OfficeChromatography/2LabsToGo-Eco-Test/2LabsToGo-Eco-Hardware/3D-Parts/STL/e-axis/e-axis_micropump_holder.stl

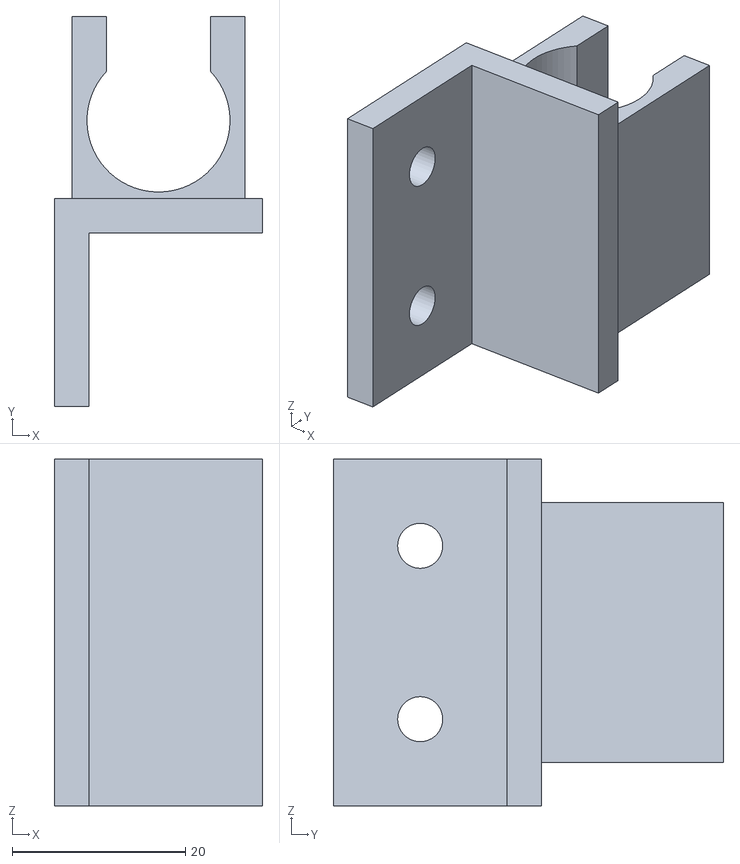
[picture p72: CAD file, 2026-04-15]
2LabsToGo-Eco-Hardware/3D-Parts/STL/e-axis/e-axis_micropump_holder.stl
24.0 x 45.0 x 40.0
