OfficeChromatography/2LabsToGo-Eco-Test/2LabsToGo-Eco-Hardware/3D-Parts/STL/electronic-box/electronic-box_frame_LED-label.stl

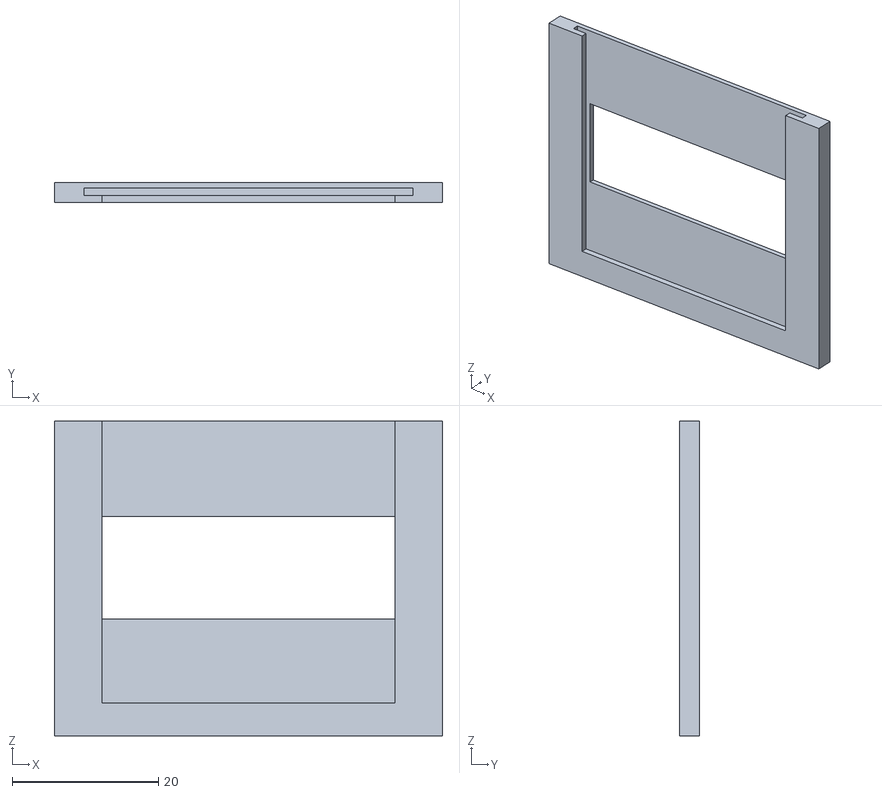
[picture p73: CAD file, 2026-04-15]
2LabsToGo-Eco-Hardware/3D-Parts/STL/electronic-box/electronic-box_frame_LED-label.stl
53.0 x 2.80 x 43.0
