OfficeChromatography/2LabsToGo-Eco-Test/2LabsToGo-Eco-Hardware/3D-Parts/STL/frames/cable_support_electronic_box.stl

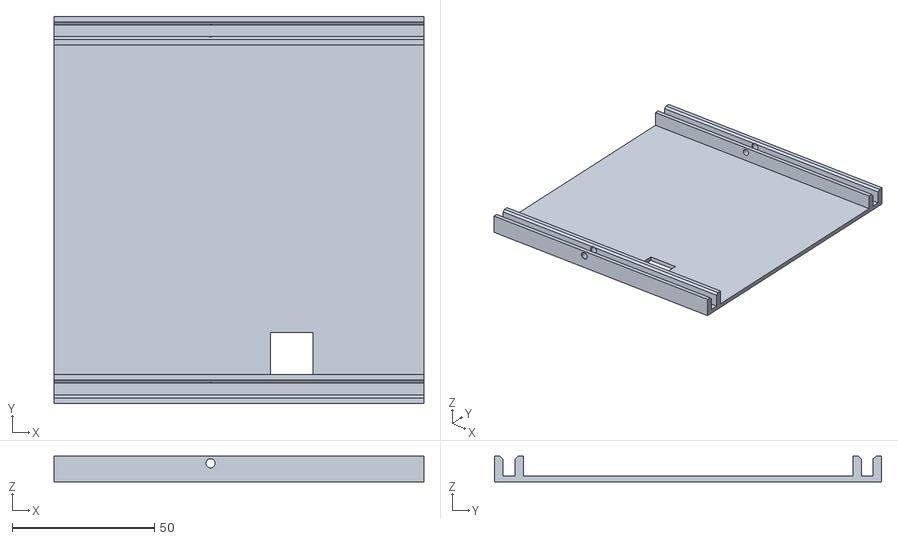
[picture p74: CAD file, 2026-04-15]
2LabsToGo-Eco-Hardware/3D-Parts/STL/frames/cable_support_electronic_box.stl
130.0 x 136.0 x 9.00
