OfficeChromatography/2LabsToGo-Eco-Test/2LabsToGo-Eco-Hardware/3D-Parts/STL/humidity-control/humidity_control_box.stl

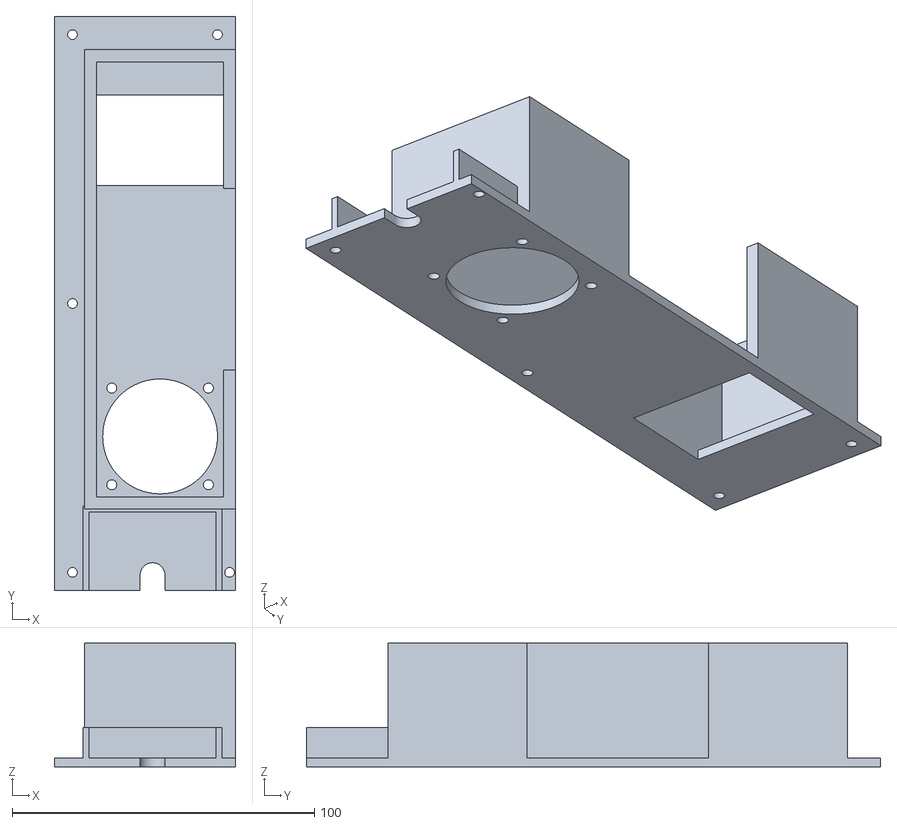
[picture p75: CAD file, 2026-04-15]
2LabsToGo-Eco-Hardware/3D-Parts/STL/humidity-control/humidity_control_box.stl
60.0 x 190.0 x 41.0
