OfficeChromatography/2LabsToGo-Eco-Test/2LabsToGo-Eco-Hardware/3D-Parts/STL/panels/cover_autosampler_z1_motor_holder.stl

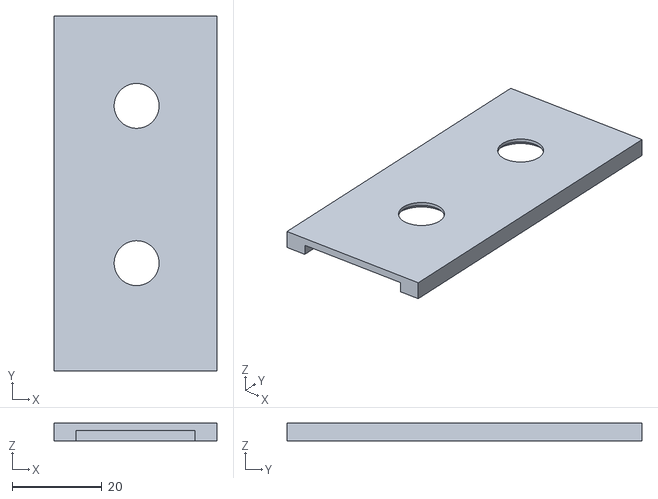
[picture p77: CAD file, 2026-04-15]
2LabsToGo-Eco-Hardware/3D-Parts/STL/panels/cover_autosampler_z1_motor_holder.stl
36.2 x 79.0 x 4.00
