OfficeChromatography/2LabsToGo-Eco-Test/2LabsToGo-Eco-Hardware/3D-Parts/STL/plate-holder/plate-holder_backlight_back.stl

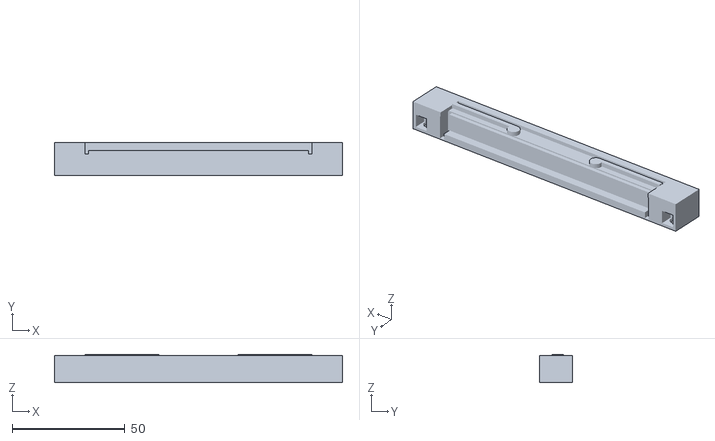
[picture p78: CAD file, 2026-04-15]
2LabsToGo-Eco-Hardware/3D-Parts/STL/plate-holder/plate-holder_backlight_back.stl
128.0 x 14.5 x 12.6
