OfficeChromatography/2LabsToGo-Eco-Test/2LabsToGo-Eco-Hardware/3D-Parts/STL/syringe-pump/syringe-pump_plug_steel_rods.stl

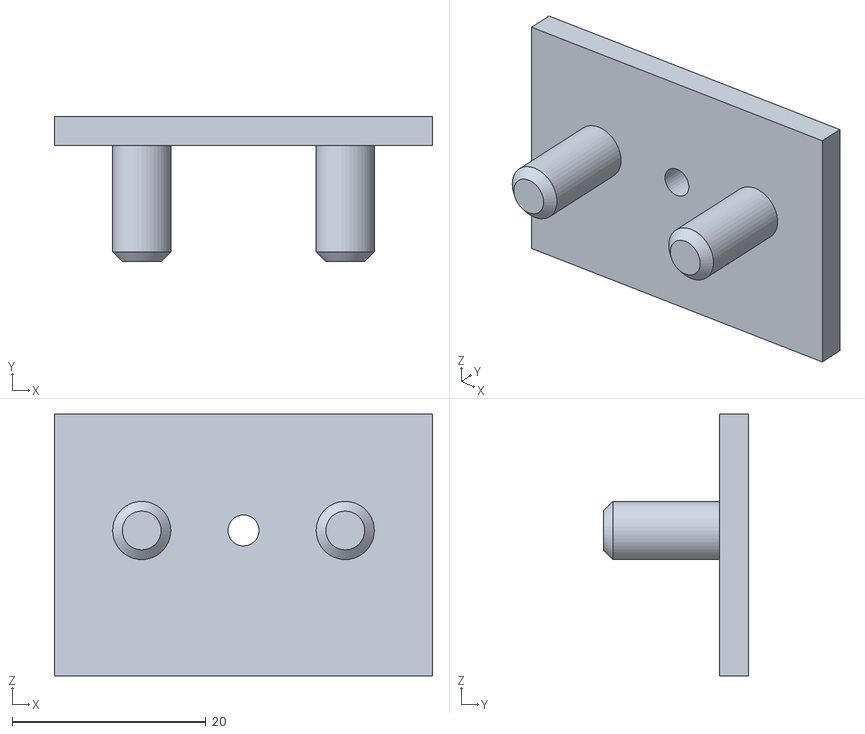
[picture p79: CAD file, 2026-04-15]
2LabsToGo-Eco-Hardware/3D-Parts/STL/syringe-pump/syringe-pump_plug_steel_rods.stl
39.0 x 15.0 x 27.0
