OfficeChromatography/2LabsToGo-Eco-Test/2LabsToGo-Eco-Hardware/3D-Parts/STL/tools/handle_allen-key_1.5mm.stl

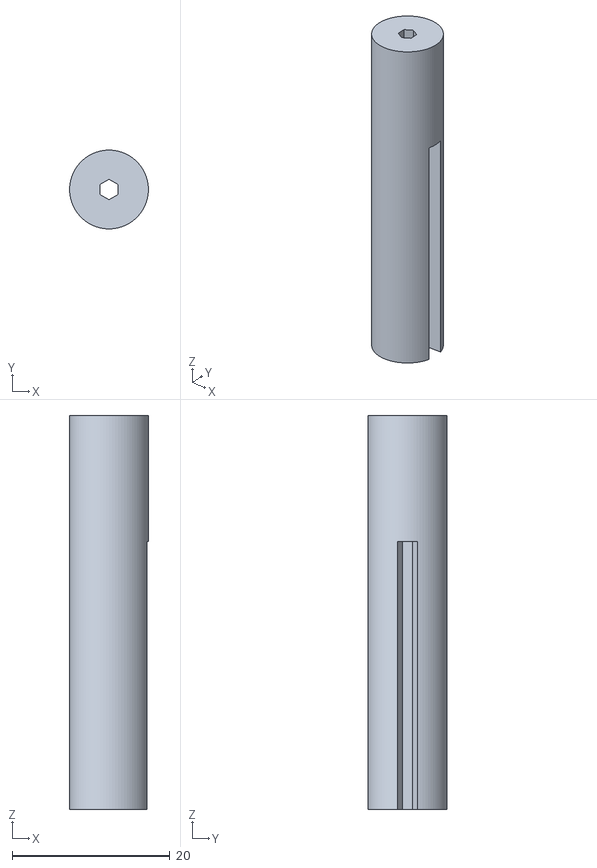
[picture p80: CAD file, 2026-04-15]
2LabsToGo-Eco-Hardware/3D-Parts/STL/tools/handle_allen-key_1.5mm.stl
10.0 x 10.0 x 50.0
