OfficeChromatography/2LabsToGo-Eco-Test/2LabsToGo-Eco-Hardware/3D-Parts/STL/x-axis/x-axis_valve_holder.stl

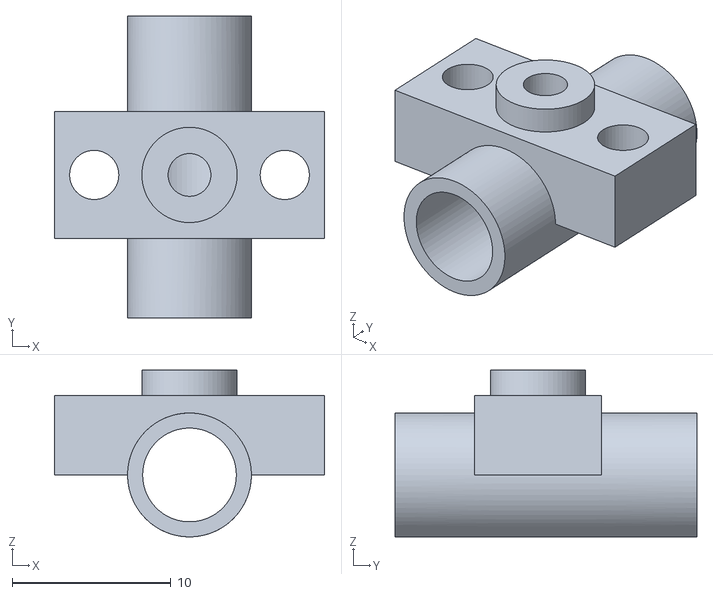
[picture p81: CAD file, 2026-04-15]
2LabsToGo-Eco-Hardware/3D-Parts/STL/x-axis/x-axis_valve_holder.stl
17.0 x 19.0 x 10.5
