OfficeChromatography/2LabsToGo-Eco-Test/2LabsToGo-Eco-Hardware/3D-Parts/STL/y-axis/y-axis_front.stl

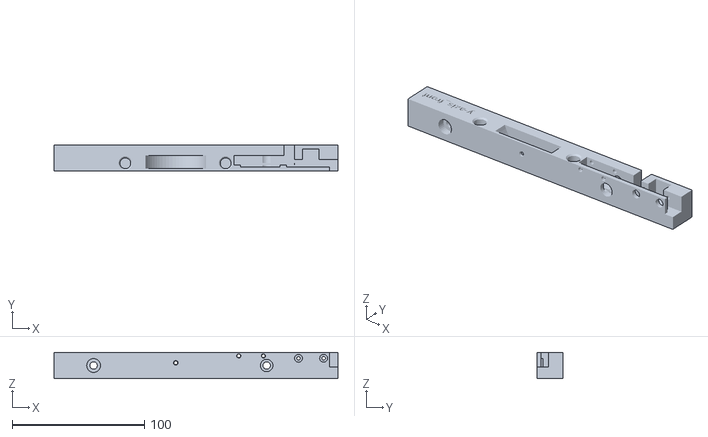
[picture p82: CAD file, 2026-04-15]
2LabsToGo-Eco-Hardware/3D-Parts/STL/y-axis/y-axis_front.stl
215.0 x 20.0 x 20.0
