OfficeChromatography/2LabsToGo-Eco-Test/2LabsToGo-Eco-Hardware/3D-Parts/DXF-panels/side_front.dxf

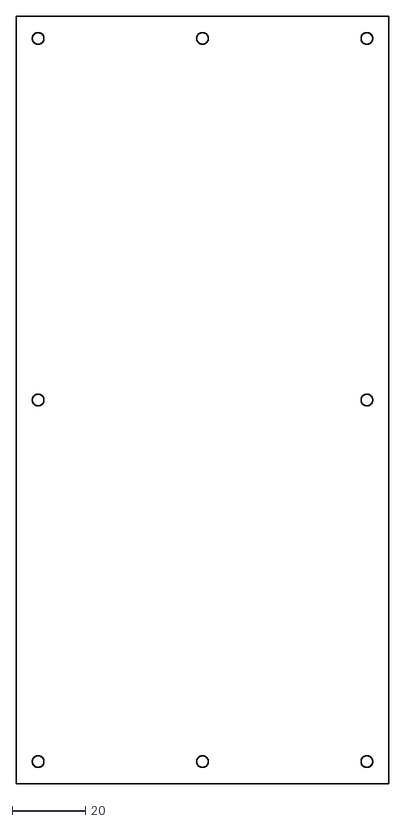
[picture p83: CAD file, 2026-04-15]
2LabsToGo-Eco-Hardware/3D-Parts/DXF-panels/side_front.dxf
102.0 x 210.0
