OfficeChromatography/2LabsToGo-Eco-Test/2LabsToGo-Eco-Hardware/3D-Parts/STL/autosampler/autosampler_slider.stl

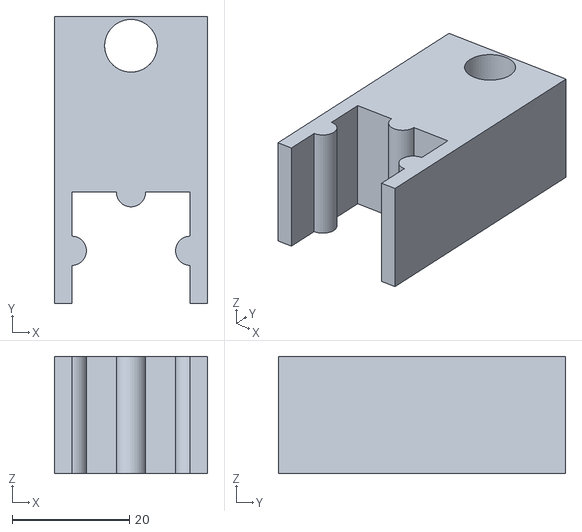
[picture p84: CAD file, 2026-04-15]
2LabsToGo-Eco-Hardware/3D-Parts/STL/autosampler/autosampler_slider.stl
26.2 x 49.0 x 20.0
