OfficeChromatography/2LabsToGo-Eco-Test/2LabsToGo-Eco-Hardware/3D-Parts/STL/camera_cabinet/camera_cabinet_UVA_filter_protect.stl

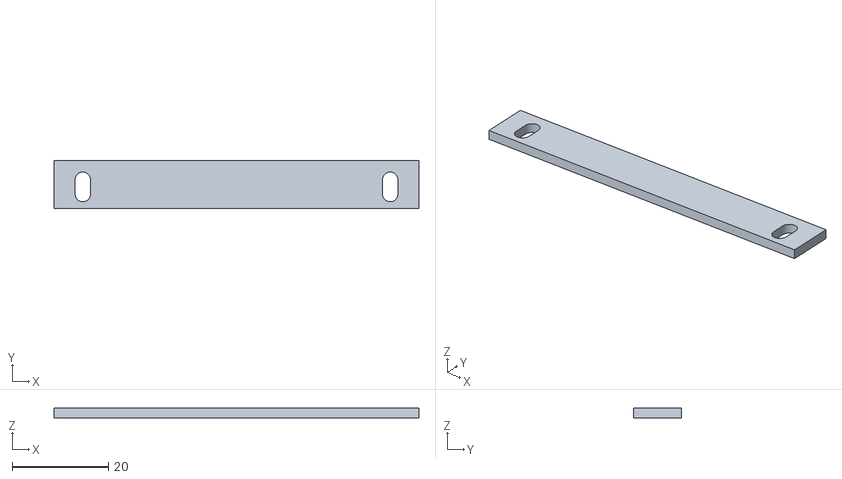
[picture p85: CAD file, 2026-04-15]
2LabsToGo-Eco-Hardware/3D-Parts/STL/camera_cabinet/camera_cabinet_UVA_filter_protect.stl
76.0 x 10.0 x 2.00
