OfficeChromatography/2LabsToGo-Eco-Test/2LabsToGo-Eco-Hardware/3D-Parts/STL/e-axis/e-axis_connector_top.stl

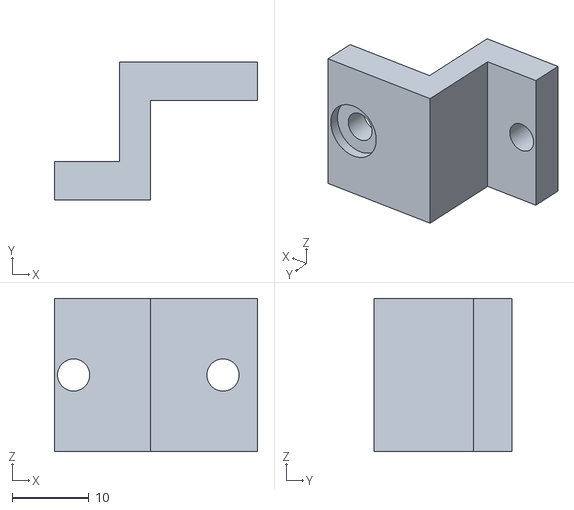
[picture p86: CAD file, 2026-04-15]
2LabsToGo-Eco-Hardware/3D-Parts/STL/e-axis/e-axis_connector_top.stl
26.5 x 18.0 x 20.0
