OfficeChromatography/2LabsToGo-Eco-Test/2LabsToGo-Eco-Hardware/3D-Parts/STL/electronic-box/electronic-box_spindle-cover.stl

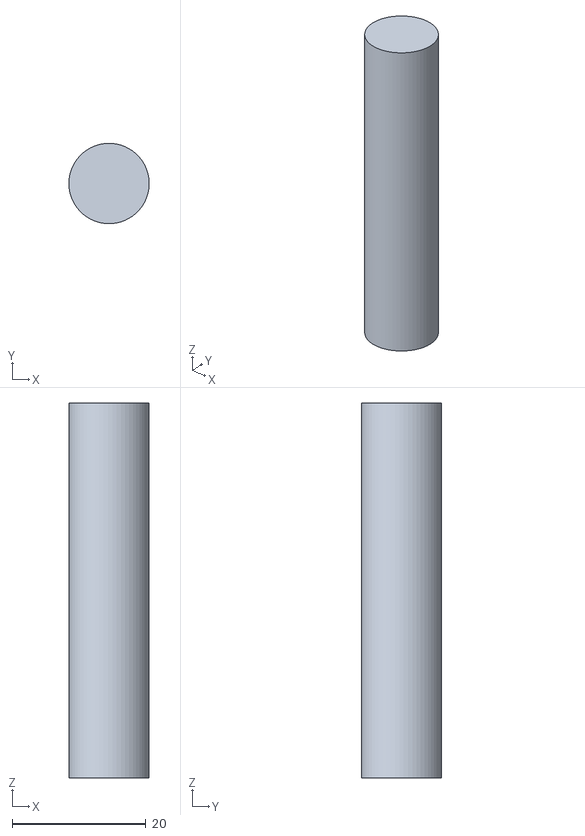
[picture p87: CAD file, 2026-04-15]
2LabsToGo-Eco-Hardware/3D-Parts/STL/electronic-box/electronic-box_spindle-cover.stl
12.0 x 12.0 x 56.0
