OfficeChromatography/2LabsToGo-Eco-Test/2LabsToGo-Eco-Hardware/3D-Parts/STL/frames/frame_left_front.stl

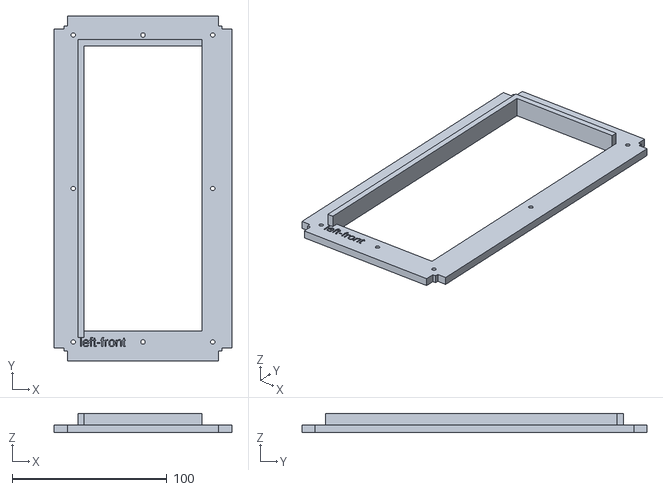
[picture p88: CAD file, 2026-04-15]
2LabsToGo-Eco-Hardware/3D-Parts/STL/frames/frame_left_front.stl
114.6 x 222.6 x 12.5
