OfficeChromatography/2LabsToGo-Eco-Test/2LabsToGo-Eco-Hardware/3D-Parts/STL/humidity-control/front_holder.stl

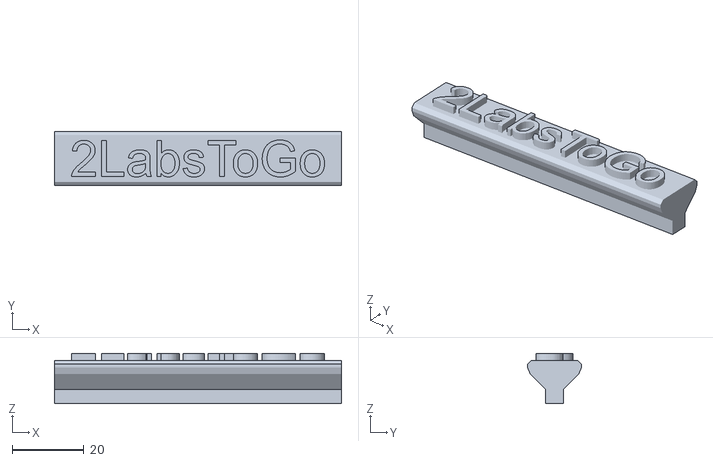
[picture p89: CAD file, 2026-04-15]
2LabsToGo-Eco-Hardware/3D-Parts/STL/humidity-control/front_holder.stl
80.0 x 15.0 x 14.0
