OfficeChromatography/2LabsToGo-Eco-Test/2LabsToGo-Eco-Hardware/3D-Parts/STL/mini-shaker/mini-shaker_motor_adapter.stl

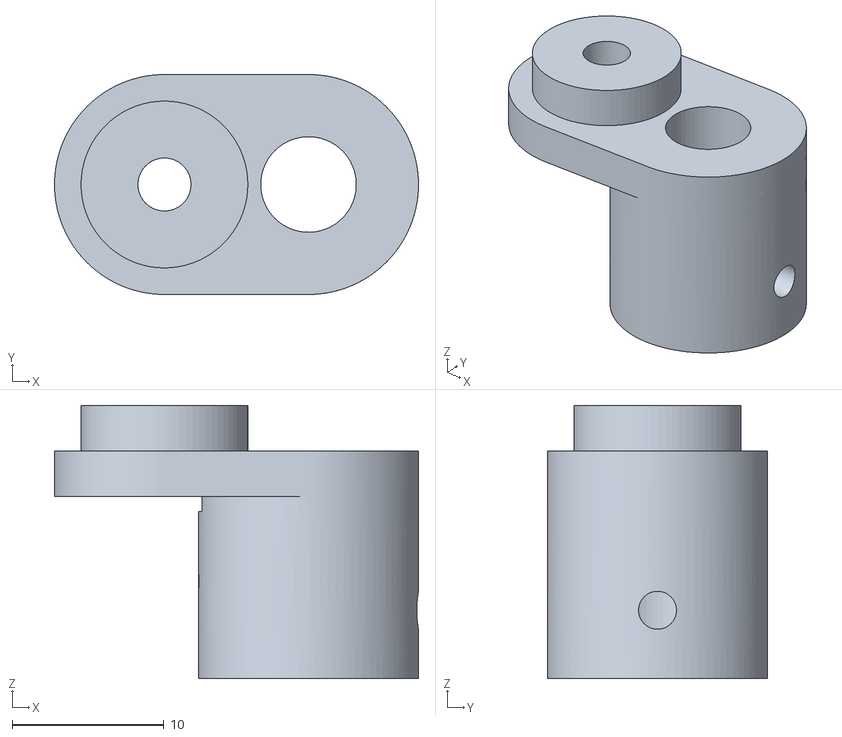
[picture p90: CAD file, 2026-04-15]
2LabsToGo-Eco-Hardware/3D-Parts/STL/mini-shaker/mini-shaker_motor_adapter.stl
24.0 x 14.5 x 18.0
