OfficeChromatography/2LabsToGo-Eco-Test/2LabsToGo-Eco-Hardware/3D-Parts/STL/nebulizer/nebulizer_chamber_extension.stl

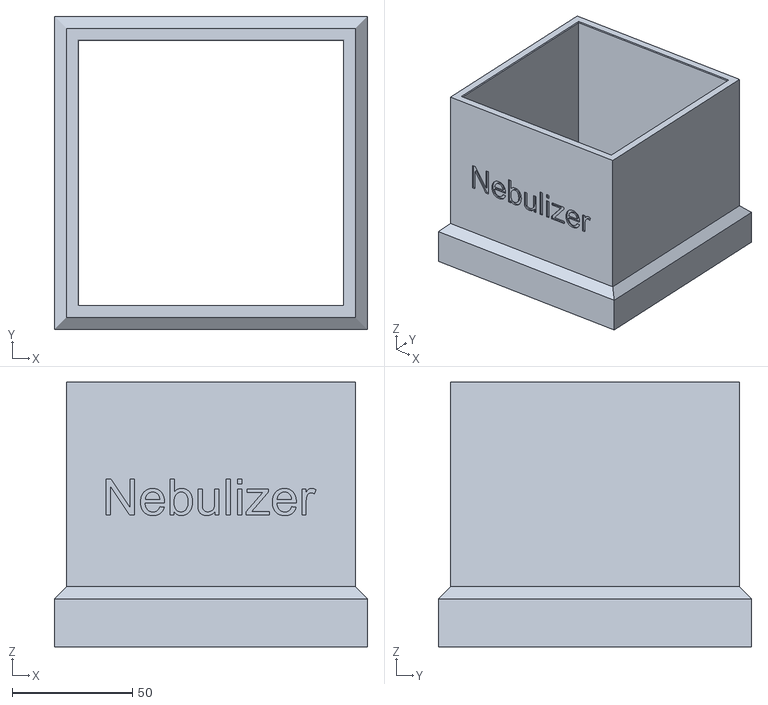
[picture p91: CAD file, 2026-04-15]
2LabsToGo-Eco-Hardware/3D-Parts/STL/nebulizer/nebulizer_chamber_extension.stl
130.0 x 130.0 x 110.0
