OfficeChromatography/2LabsToGo-Eco-Test/2LabsToGo-Eco-Hardware/3D-Parts/STL/tools/test-tool_cube-magnet.stl

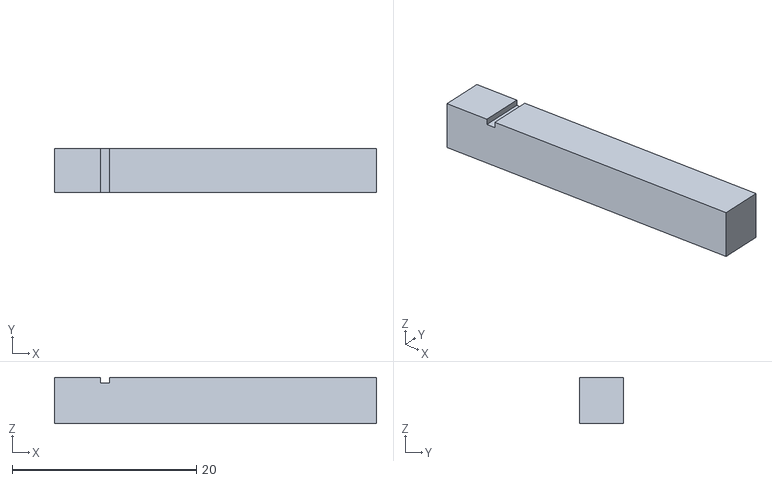
[picture p94: CAD file, 2026-04-15]
2LabsToGo-Eco-Hardware/3D-Parts/STL/tools/test-tool_cube-magnet.stl
35.0 x 4.80 x 5.00
