OfficeChromatography/2LabsToGo-Eco-Test/2LabsToGo-Eco-Hardware/3D-Parts/STL/autosampler/autosampler_vialrack.stl

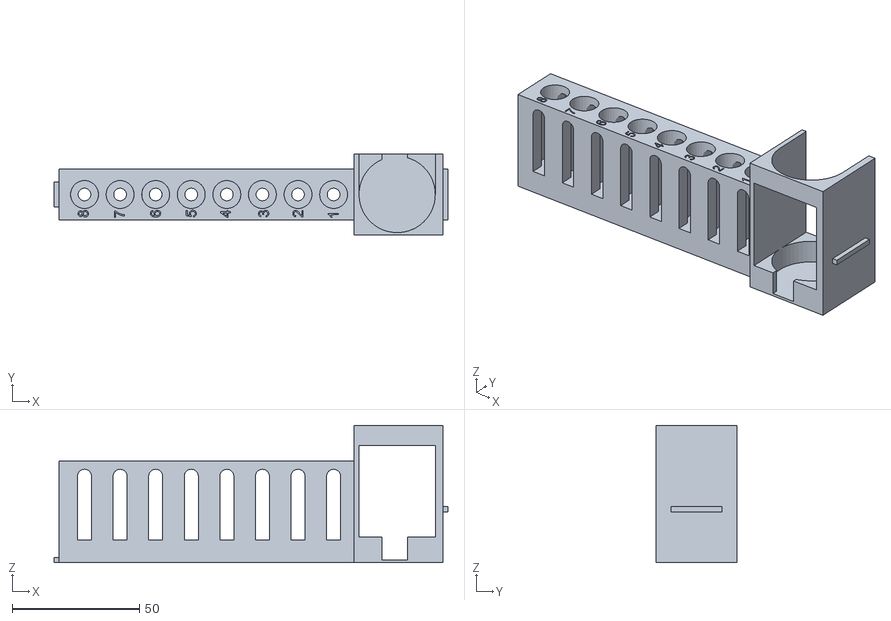
[picture p97: CAD file, 2026-04-15]
2LabsToGo-Eco-Hardware/3D-Parts/STL/autosampler/autosampler_vialrack.stl
155.0 x 32.0 x 54.0
