OfficeChromatography/2LabsToGo-Eco-Test/2LabsToGo-Eco-Hardware/3D-Parts/STL/e-axis/3way-valve_manifold.stl

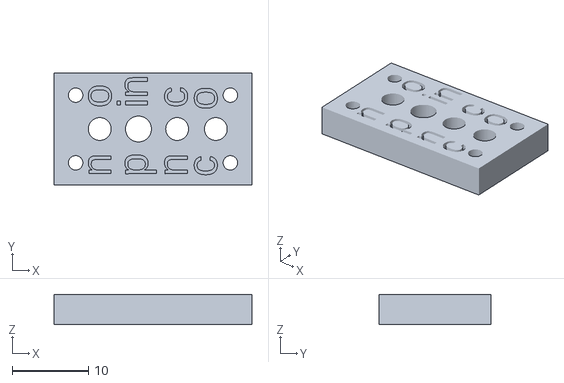
[picture p98: CAD file, 2026-04-15]
2LabsToGo-Eco-Hardware/3D-Parts/STL/e-axis/3way-valve_manifold.stl
26.0 x 14.7 x 4.00
