OfficeChromatography/2LabsToGo-Eco-Test/2LabsToGo-Eco-Hardware/3D-Parts/STL/frames/cable_clip1.stl

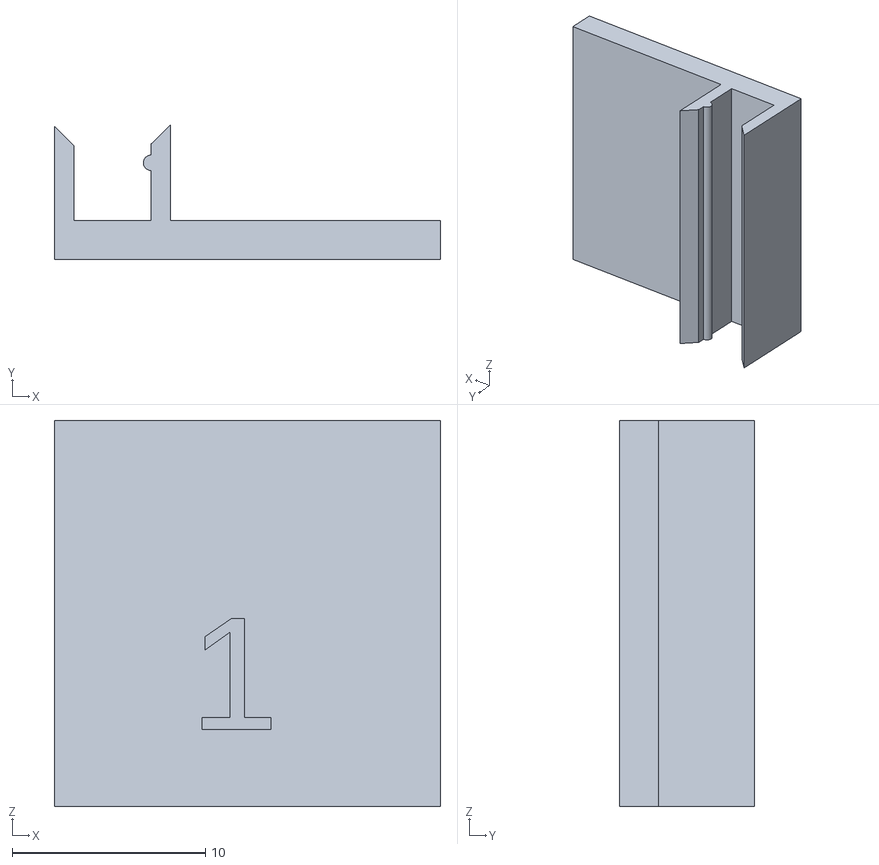
[picture p99: CAD file, 2026-04-15]
2LabsToGo-Eco-Hardware/3D-Parts/STL/frames/cable_clip1.stl
20.0 x 6.97 x 20.0
