OfficeChromatography/2LabsToGo-Eco-Test/2LabsToGo-Eco-Hardware/3D-Parts/STL/mini-shaker/mini-shaker_burling.stl

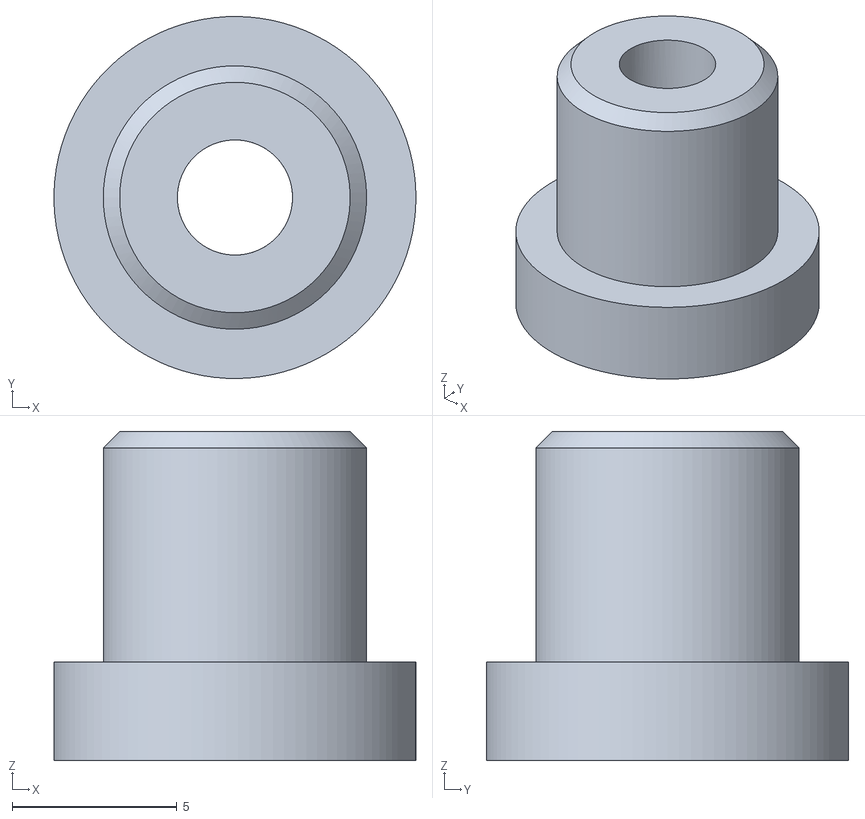
[picture p100: CAD file, 2026-04-15]
2LabsToGo-Eco-Hardware/3D-Parts/STL/mini-shaker/mini-shaker_burling.stl
11.0 x 11.0 x 10.0
