OfficeChromatography/2LabsToGo-Eco-Test/2LabsToGo-Eco-Hardware/3D-Parts/STL/panels/waste_bottle_holder.stl

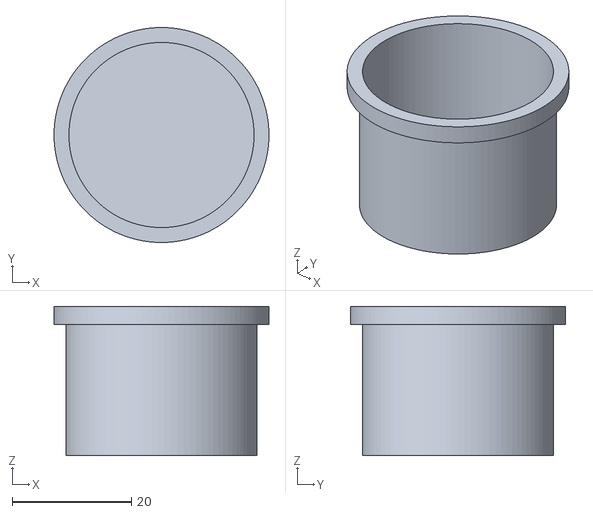
[picture p101: CAD file, 2026-04-15]
2LabsToGo-Eco-Hardware/3D-Parts/STL/panels/waste_bottle_holder.stl
36.0 x 36.0 x 25.0
