OfficeChromatography/2LabsToGo-Eco-Test/2LabsToGo-Eco-Hardware/3D-Parts/STL/syringe-pump/syringe-pump_pusher_syringe_adapter_10mL.stl

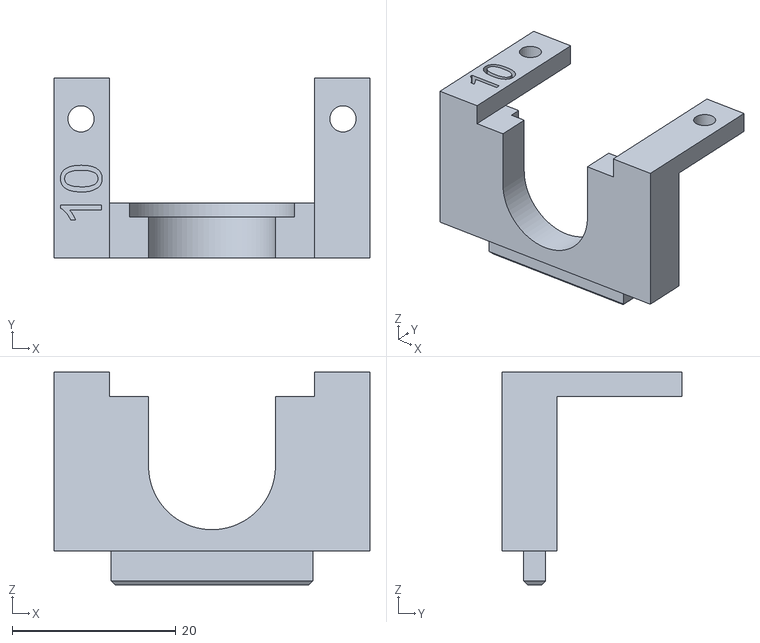
[picture p103: CAD file, 2026-04-15]
2LabsToGo-Eco-Hardware/3D-Parts/STL/syringe-pump/syringe-pump_pusher_syringe_adapter_10mL.stl
38.6 x 22.0 x 26.0
