OfficeChromatography/2LabsToGo-Eco-Test/2LabsToGo-Eco-Hardware/3D-Parts/STL/panels/cover_y_motor.stl

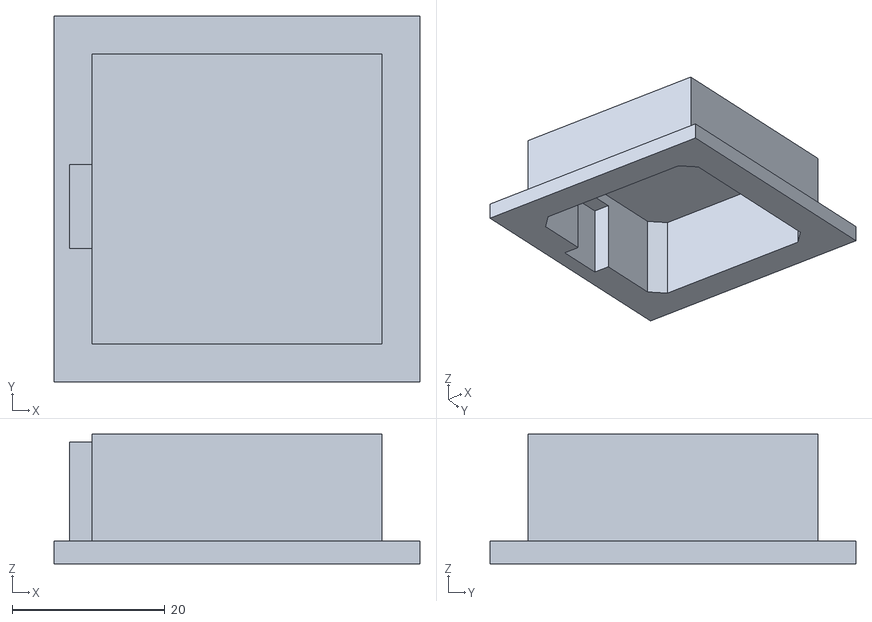
[picture p109: CAD file, 2026-04-15]
2LabsToGo-Eco-Hardware/3D-Parts/STL/panels/cover_y_motor.stl
48.0 x 48.0 x 17.0
