OfficeChromatography/2LabsToGo-Eco-Test/2LabsToGo-Eco-Hardware/3D-Parts/STL/plate-holder/plate-holder_backlight_plug.stl

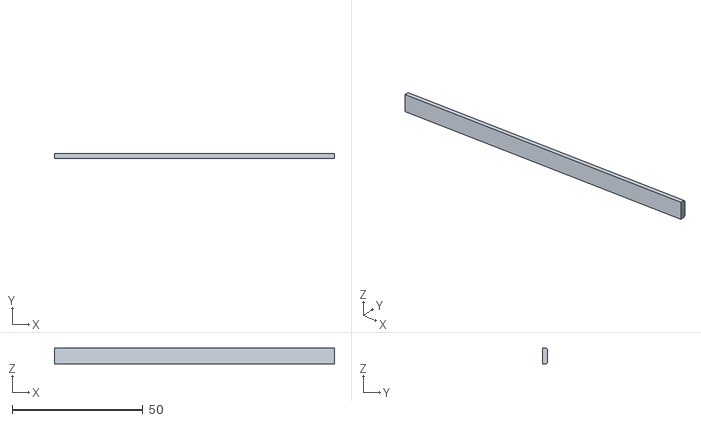
[picture p110: CAD file, 2026-04-15]
2LabsToGo-Eco-Hardware/3D-Parts/STL/plate-holder/plate-holder_backlight_plug.stl
107.0 x 2.00 x 6.00
