OfficeChromatography/2LabsToGo-Eco-Test/2LabsToGo-Eco-Hardware/3D-Parts/STL/tools/test-tool_round-magnet.stl

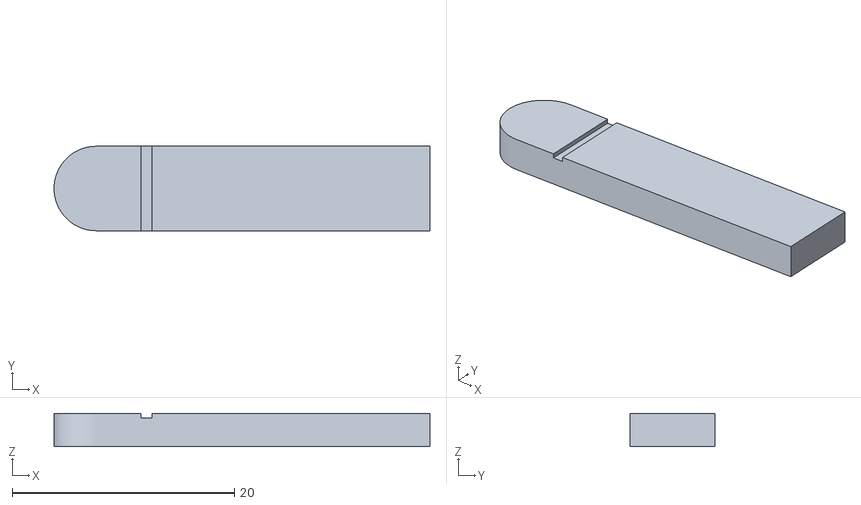
[picture p112: CAD file, 2026-04-15]
2LabsToGo-Eco-Hardware/3D-Parts/STL/tools/test-tool_round-magnet.stl
33.8 x 7.60 x 3.00
