OfficeChromatography/2LabsToGo-Eco-Test/2LabsToGo-Eco-Hardware/3D-Parts/STL/e-axis/micropump_manifold_drill-aid.stl

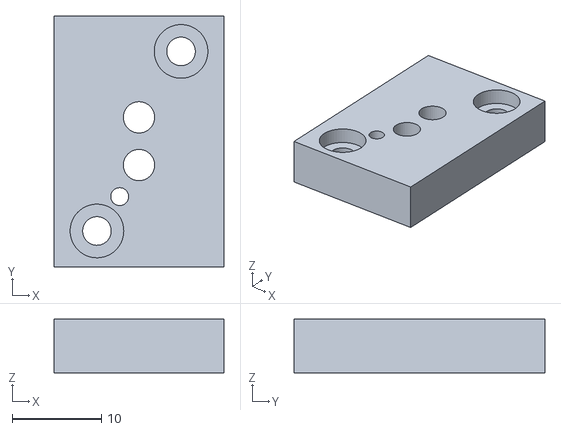
[picture p115: CAD file, 2026-04-15]
2LabsToGo-Eco-Hardware/3D-Parts/STL/e-axis/micropump_manifold_drill-aid.stl
19.0 x 28.0 x 6.00
