OfficeChromatography/2LabsToGo-Eco-Test/2LabsToGo-Eco-Hardware/3D-Parts/STL/plate-holder/multifunctional_plate-holder_plug.stl

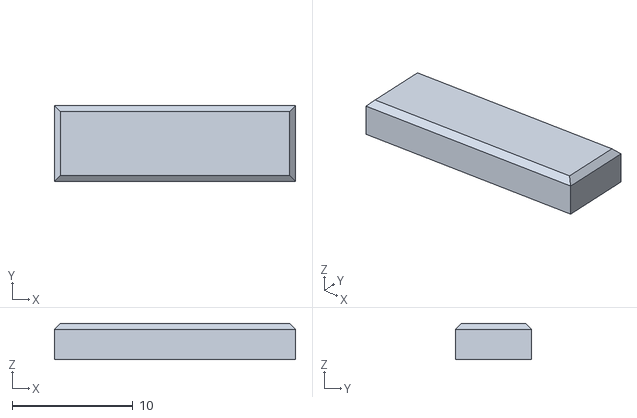
[picture p118: CAD file, 2026-04-15]
2LabsToGo-Eco-Hardware/3D-Parts/STL/plate-holder/multifunctional_plate-holder_plug.stl
20.0 x 6.30 x 3.00
