OfficeChromatography/2LabsToGo-Eco-Test/2LabsToGo-Eco-Hardware/3D-Parts/STL/tools/handle_for_thread_tap_M2.5.stl

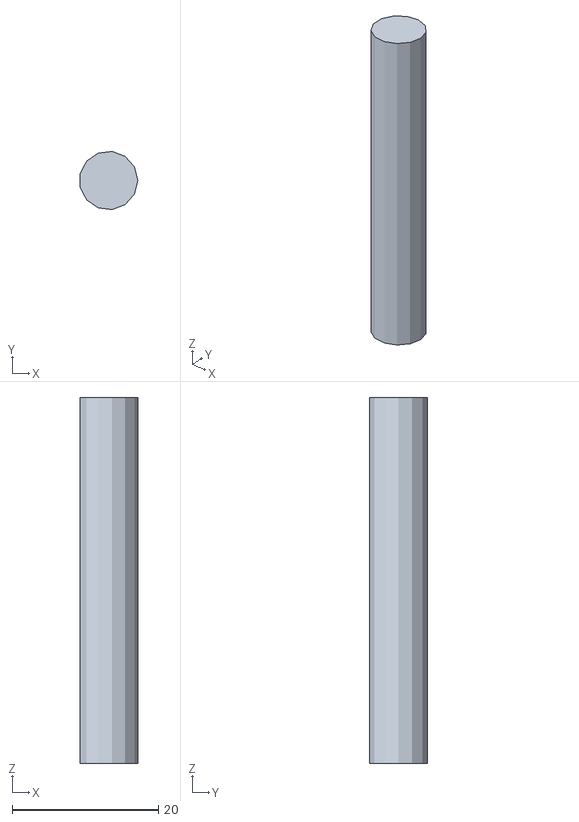
[picture p129: CAD file, 2026-04-15]
2LabsToGo-Eco-Hardware/3D-Parts/STL/tools/handle_for_thread_tap_M2.5.stl
7.88 x 7.94 x 50.0
