OfficeChromatography/2LabsToGo-Eco-Test/2LabsToGo-Eco-Hardware/3D-Parts/STL/frames/cable_clip_alu.stl

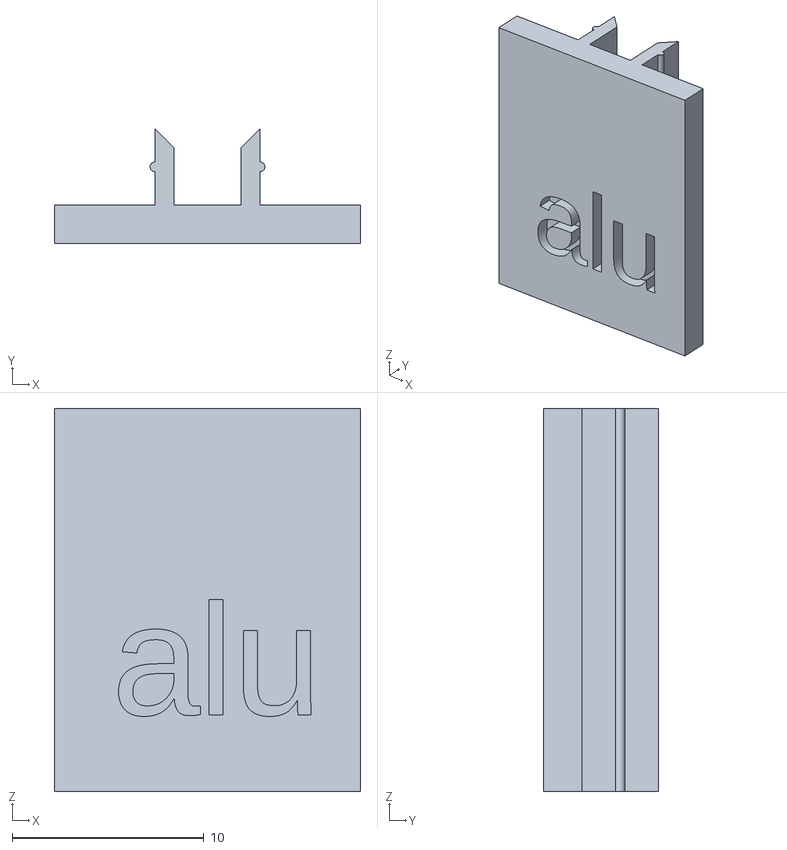
[picture p134: CAD file, 2026-04-15]
2LabsToGo-Eco-Hardware/3D-Parts/STL/frames/cable_clip_alu.stl
16.0 x 6.00 x 20.0
